rcslon3-svg/DOGS2_v1/assets/photos/all_you_need.jpg

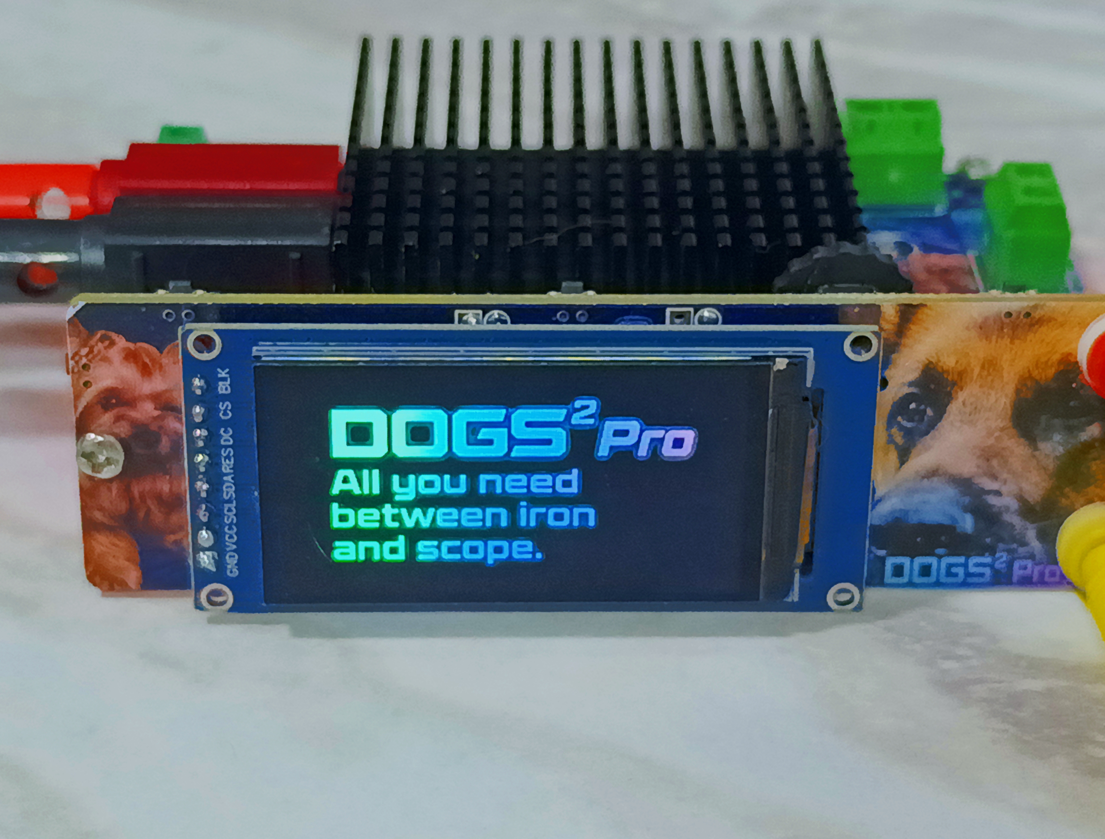
assets/photos/all_you_need.jpg
