rcslon3-svg/DOGS2_v1/assets/photos/connect.jpg

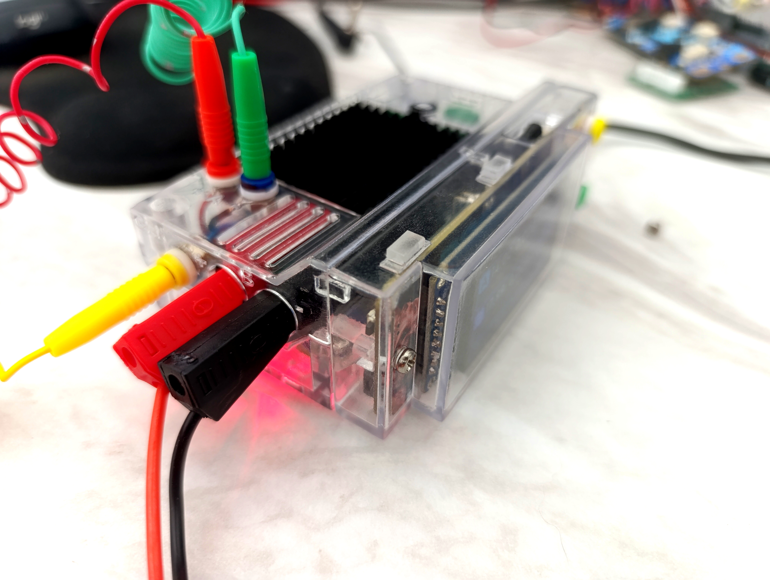
assets/photos/connect.jpg
