rcslon3-svg/DOGS2_v1/assets/photos/dogs2-signal-generator.jpg

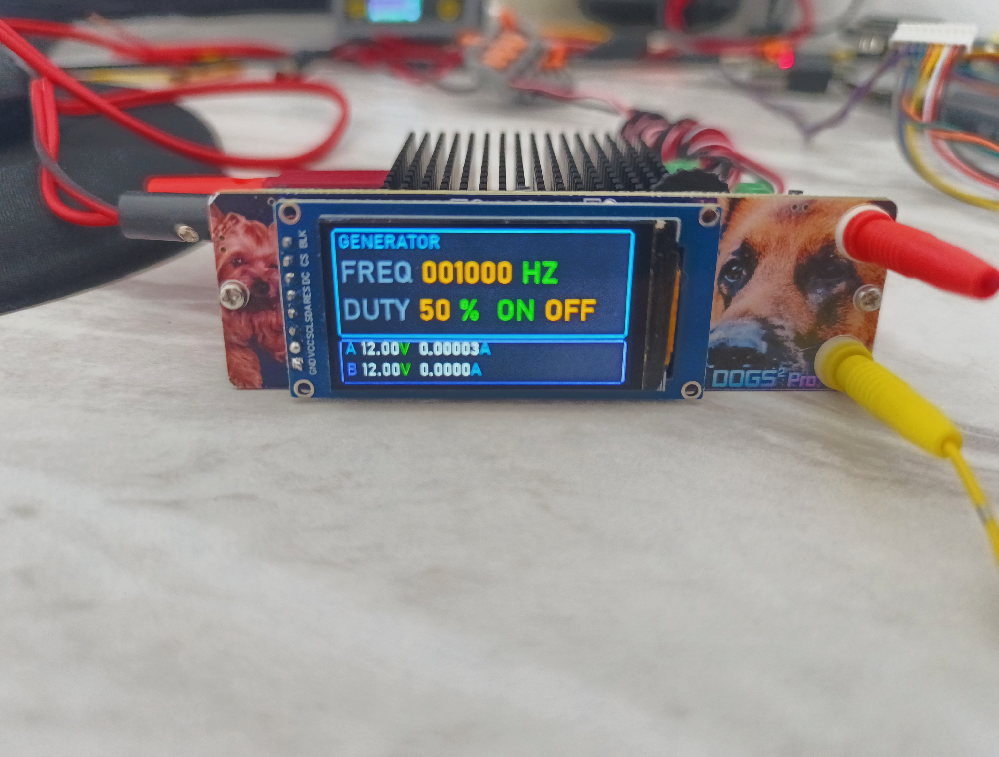
assets/photos/dogs2-signal-generator.jpg
