rcslon3-svg/DOGS2_v1/assets/photos/dogs2-working-prototype-front.png

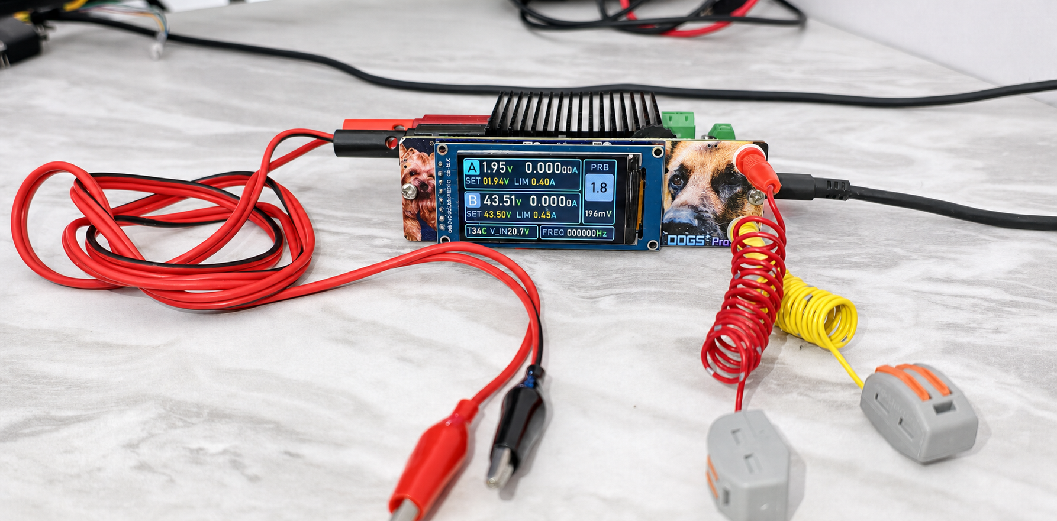
assets/photos/dogs2-working-prototype-front.png
