rcslon3-svg/DOGS2_v1/assets/photos/generator_display.jpg

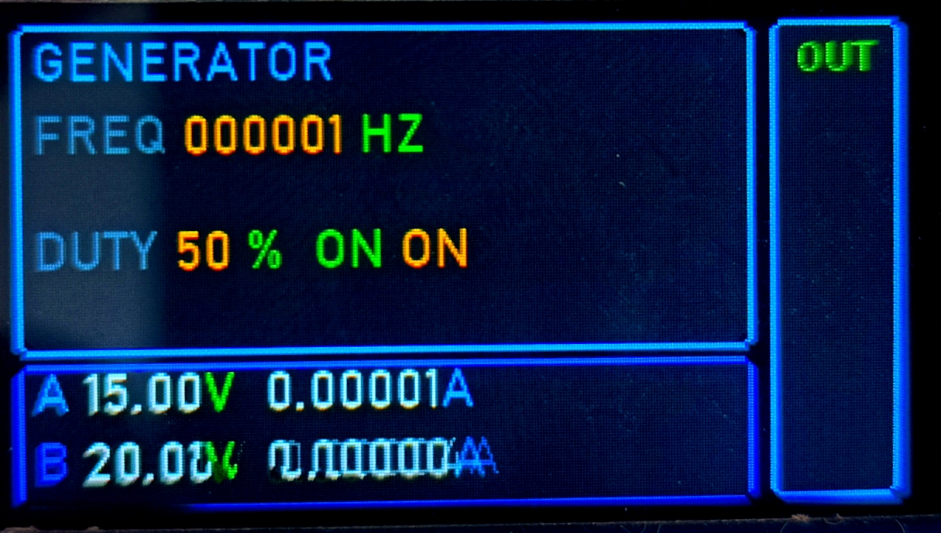
assets/photos/generator_display.jpg
