rcslon3-svg/DOGS2_v1/assets/photos/power_bottom.jpg

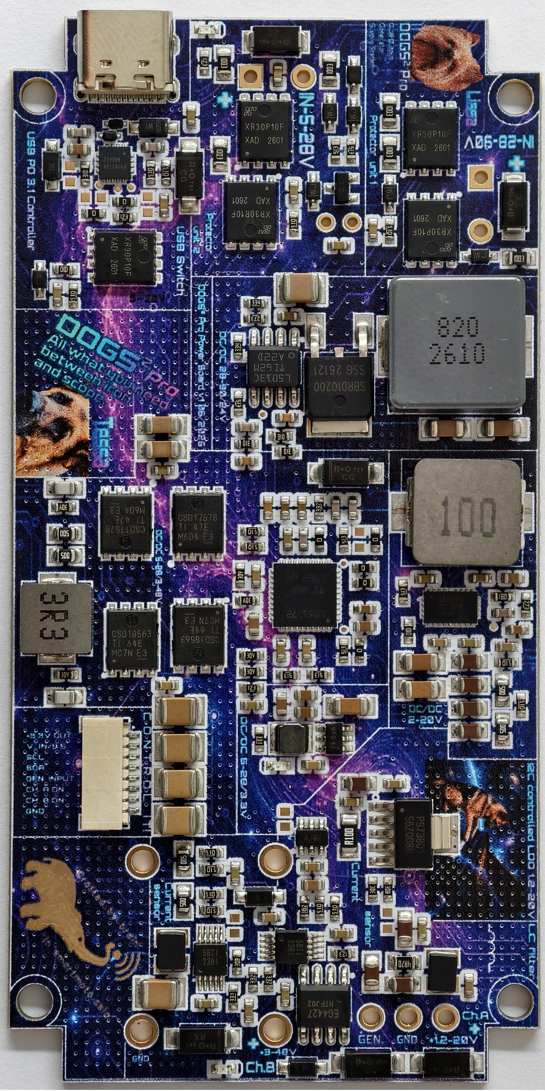
assets/photos/power_bottom.jpg
