rcslon3-svg/DOGS2_v1/assets/photos/power_bottom_90deg_40perc.jpg

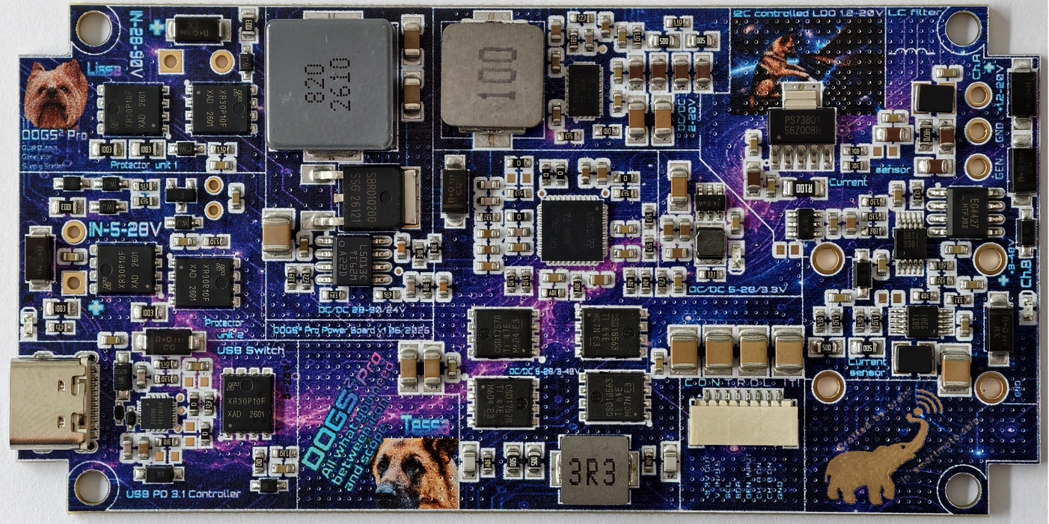
assets/photos/power_bottom_90deg_40perc.jpg
