rcslon3-svg/DOGS2_v1/assets/photos/power_source_display.jpg

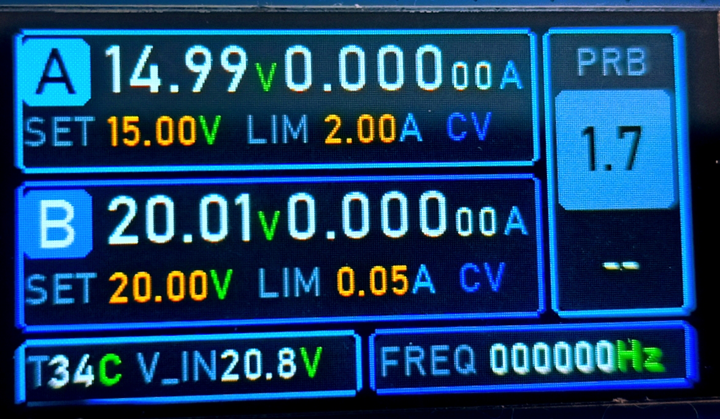
assets/photos/power_source_display.jpg
