rcslon3-svg/DOGS2_v1/assets/photos/rs485_display.jpg

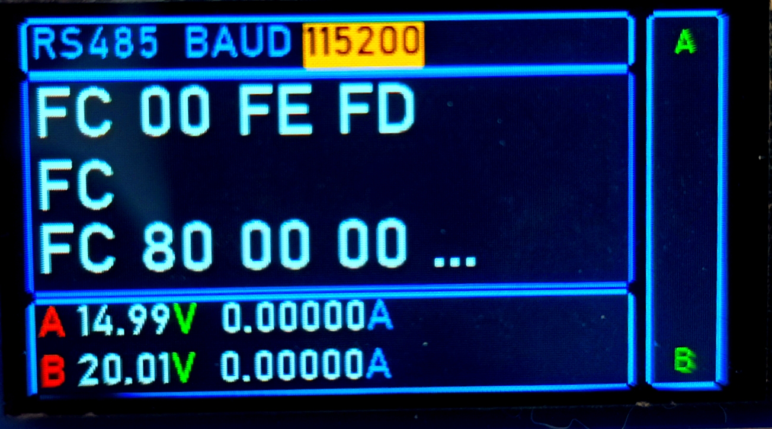
assets/photos/rs485_display.jpg
