rcslon3-svg/DOGS2_v1/assets/photos/uart_display.jpg

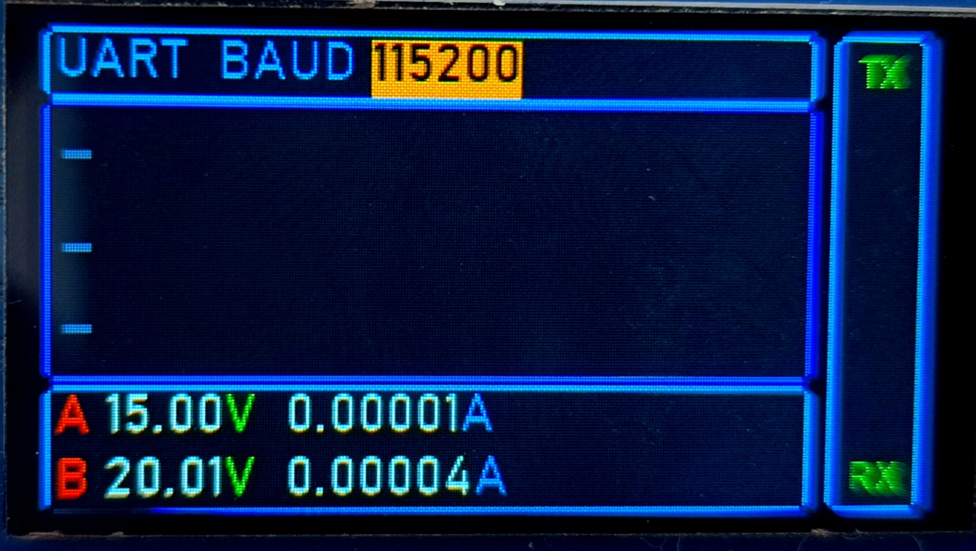
assets/photos/uart_display.jpg
