rcslon3-svg/DOGS2_v1/software/assets/dogs2-pro-all-you-need-transparent.png

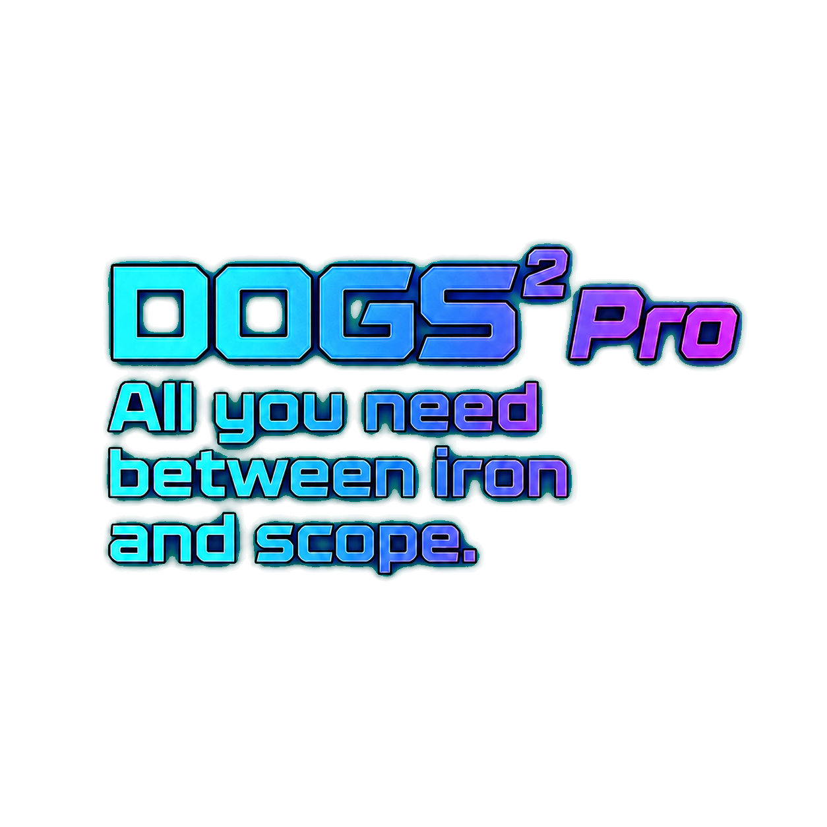
software/assets/dogs2-pro-all-you-need-transparent.png
