rcslon3-svg/DOGS2_v1/software/src/display.c

#include "display.h"

#include <stdarg.h>
#include <stdio.h>
#include <string.h>
#include "driver/gpio.h"
#include "driver/ledc.h"
#include "driver/spi_master.h"
#include "calibration.h"
#include "current_graph.h"
#include "esp_check.h"
#include "esp_log.h"
#include "esp_timer.h"
#include "freertos/FreeRTOS.h"
#include "freertos/task.h"
#include "probe_config.h"
#include "smooth_font.h"
#include "splash_bitmap.h"

#define RGB565(r, g, b) (uint16_t)((((r) & 0xF8U) << 8) | (((g) & 0xFCU) << 3) | ((b) >> 3))
#define COLOR_BLACK RGB565(0, 0, 0)
#define COLOR_WHITE RGB565(255, 255, 255)
#define COLOR_GREEN RGB565(40, 230, 90)
#define COLOR_RED RGB565(255, 45, 35)
#define COLOR_BLUE RGB565(30, 80, 255)
#define COLOR_YELLOW RGB565(255, 210, 0)
#define COLOR_CYAN RGB565(0, 210, 255)
#define COLOR_PURPLE RGB565(169, 92, 255)
#define COLOR_ORANGE RGB565(255, 120, 0)
#define COLOR_GRAY RGB565(155, 165, 180)
#define COLOR_LABEL RGB565(205, 215, 230)
#define COLOR_PANEL RGB565(9, 12, 18)
#define COLOR_BADGE_CV_FG COLOR_WHITE
#define COLOR_BADGE_CV_BG RGB565(18, 18, 18)
#define COLOR_BADGE_CC_FG COLOR_BLACK
#define COLOR_BADGE_CC_BG RGB565(0, 210, 220)
#define COLOR_ALERT_RED_FG COLOR_WHITE
#define COLOR_ALERT_RED_BG COLOR_RED
#define POWER_CHANNEL_FRAME_X 6
#define POWER_CHANNEL_FRAME_WIDTH 238
#define POWER_CHANNEL_INNER_X 8
#define POWER_CHANNEL_INNER_RIGHT 242
#define DISPLAY_CALIBRATION_SAMPLE_COUNT 32U
#define POWER_CURRENT_RIGHT 238
#define POWER_SIDE_FRAME_X 248
#define POWER_SIDE_FRAME_WIDTH 66
#define INTERFACE_MAIN_FRAME_WIDTH 268
#define INTERFACE_MAIN_INNER_RIGHT 272
#define INTERFACE_SIDE_FRAME_X 280
#define INTERFACE_SIDE_FRAME_WIDTH 34
#define INTERFACE_SIDE_INNER_X (INTERFACE_SIDE_FRAME_X + 2)
#define INTERFACE_SIDE_INNER_RIGHT \
    (INTERFACE_SIDE_FRAME_X + INTERFACE_SIDE_FRAME_WIDTH - 2)
#define CURRENT_GRAPH_X 10
#define CURRENT_GRAPH_Y 30
#define CURRENT_GRAPH_W 258
#define CURRENT_GRAPH_H 90
#define CURRENT_GRAPH_SAMPLES_PER_DIV 20
#define CURRENT_GRAPH_CELLS_Y 5
#define CURRENT_GRAPH_BASE_SAMPLE_MS 100U
#define TFT_BACKLIGHT_LEDC_MODE LEDC_HIGH_SPEED_MODE
#define TFT_BACKLIGHT_LEDC_TIMER LEDC_TIMER_3
#define TFT_BACKLIGHT_LEDC_CHANNEL LEDC_CHANNEL_7
#define TFT_BACKLIGHT_LEDC_RESOLUTION LEDC_TIMER_10_BIT
#define TFT_BACKLIGHT_LEDC_HZ 20000U
#define TFT_BACKLIGHT_DUTY_MAX ((1U << 10U) - 1U)
#define TFT_BACKLIGHT_FADE_MS 800U
#define TFT_BACKLIGHT_FADE_STEPS 32U
#define TFT_SPLASH_VISIBLE_MS 2000U
#define DISPLAY_BUFFER_ROWS 40U
#define DISPLAY_CURRENT_AVG_SAMPLES 3U

static spi_device_handle_t s_tft;
static const char *TAG = "display";
static int s_graph_slice_y;
static int s_graph_slice_h;

/*
 * Text is composed in RAM before it is sent to the TFT.  Besides allowing
 * four-bit antialiasing, this is important for a measurement instrument:
 * clearing and drawing a line in separate SPI operations made the old 5x7
 * font visibly blink.  A 320 x 40 buffer costs 25.6 kB but each completed
 * line now reaches the display as one continuous image.
 */
static uint16_t s_text_buffer[TFT_WIDTH * DISPLAY_BUFFER_ROWS];
static uint8_t s_fill_block[4096];

/* Match the pixel polarity already used by the working splash bitmap. */
static uint16_t display_pixel(uint16_t logical_color)
{
    uint16_t wire_color = (uint16_t)(logical_color ^ 0xFFFFU);
    return (uint16_t)((wire_color << 8) | (wire_color >> 8));
}

static void clear_text_buffer(int height, uint16_t logical_color)
{
    uint16_t pixel = display_pixel(logical_color);
    size_t count = (size_t)TFT_WIDTH * (size_t)height;
    for (size_t i = 0U; i < count; ++i) s_text_buffer[i] = pixel;
}

static uint32_t backlight_physical_duty(uint32_t logical_duty)
{
    if (logical_duty > TFT_BACKLIGHT_DUTY_MAX) logical_duty = TFT_BACKLIGHT_DUTY_MAX;
    return TFT_BACKLIGHT_ACTIVE_LEVEL ? logical_duty : (TFT_BACKLIGHT_DUTY_MAX - logical_duty);
}

static esp_err_t backlight_pwm_set(uint32_t logical_duty)
{
    esp_err_t err = ledc_set_duty(TFT_BACKLIGHT_LEDC_MODE,
                                  TFT_BACKLIGHT_LEDC_CHANNEL,
                                  backlight_physical_duty(logical_duty));
    if (err != ESP_OK) return err;
    return ledc_update_duty(TFT_BACKLIGHT_LEDC_MODE, TFT_BACKLIGHT_LEDC_CHANNEL);
}

static esp_err_t backlight_pwm_init(void)
{
    ledc_timer_config_t timer = {
        .speed_mode = TFT_BACKLIGHT_LEDC_MODE,
        .timer_num = TFT_BACKLIGHT_LEDC_TIMER,
        .duty_resolution = TFT_BACKLIGHT_LEDC_RESOLUTION,
        .freq_hz = TFT_BACKLIGHT_LEDC_HZ,
        .clk_cfg = LEDC_AUTO_CLK,
    };
    ESP_RETURN_ON_ERROR(ledc_timer_config(&timer), TAG, "backlight timer");

    ledc_channel_config_t channel = {
        .gpio_num = TFT_BACKLIGHT_GPIO,
        .speed_mode = TFT_BACKLIGHT_LEDC_MODE,
        .channel = TFT_BACKLIGHT_LEDC_CHANNEL,
        .intr_type = LEDC_INTR_DISABLE,
        .timer_sel = TFT_BACKLIGHT_LEDC_TIMER,
        .duty = backlight_physical_duty(0U),
        .hpoint = 0,
        .flags = {
            .output_invert = 0,
        },
    };
    return ledc_channel_config(&channel);
}

static void backlight_fade_in(void)
{
    const TickType_t step_delay = pdMS_TO_TICKS(TFT_BACKLIGHT_FADE_MS / TFT_BACKLIGHT_FADE_STEPS);
    for (uint32_t step = 0U; step <= TFT_BACKLIGHT_FADE_STEPS; ++step) {
        uint32_t duty = (TFT_BACKLIGHT_DUTY_MAX * step) / TFT_BACKLIGHT_FADE_STEPS;
        esp_err_t err = backlight_pwm_set(duty);
        if (err != ESP_OK) {
            ESP_LOGE(TAG, "backlight duty: %s", esp_err_to_name(err));
            return;
        }
        if (step < TFT_BACKLIGHT_FADE_STEPS) vTaskDelay(step_delay);
    }
}

static void log_pin_levels(const char *stage)
{
    ESP_LOGI(TAG, "%s pins: SCL=%d SDA=%d RES=%d DC=%d CS=%d BLK=%d",
             stage,
             gpio_get_level(TFT_SCLK_GPIO),
             gpio_get_level(TFT_MOSI_GPIO),
             gpio_get_level(TFT_RESET_GPIO),
             gpio_get_level(TFT_DC_GPIO),
             gpio_get_level(TFT_CS_GPIO),
             gpio_get_level(TFT_BACKLIGHT_GPIO));
}

/* send
 * Inputs: data selects command/data mode; bytes/length point to SPI payload.
 * Returns: none.
 * Does: sends one blocking SPI transaction to the TFT.
 */
static void send(bool data, const void *bytes, size_t length)
{
    if (s_tft == NULL) return;
    gpio_set_level(TFT_DC_GPIO, data ? 1 : 0);
    spi_transaction_t transaction = {
        .length = length * 8U,
        .tx_buffer = bytes
    };
    esp_err_t err = spi_device_polling_transmit(s_tft, &transaction);
    if (err != ESP_OK) ESP_LOGE(TAG, "spi tx: %s", esp_err_to_name(err));
}

/* command
 * Inputs: value is one ST7789 command byte.
 * Returns: none.
 * Does: sends a display command byte without parameters.
 */
static void command(uint8_t value)
{
    send(false, &value, 1U);
}

/* command_data
 * Inputs: cmd is the command byte; data/length are optional parameters.
 * Returns: none.
 * Does: sends one ST7789 command followed by its data bytes.
 */
static void command_data(uint8_t cmd, const uint8_t *data, size_t length)
{
    command(cmd);
    if (length != 0U) send(true, data, length);
}

/* set_window
 * Inputs: x/y/width/height describe the rectangular TFT write area.
 * Returns: none.
 * Does: programs the ST7789 column/page address window.
 */
static void set_window(int x, int y, int width, int height)
{
    x += TFT_X_OFFSET;
    y += TFT_Y_OFFSET;
    uint16_t x2 = (uint16_t)(x + width - 1);
    uint16_t y2 = (uint16_t)(y + height - 1);
    uint8_t cols[] = {(uint8_t)(x >> 8), (uint8_t)x, (uint8_t)(x2 >> 8), (uint8_t)x2};
    uint8_t rows[] = {(uint8_t)(y >> 8), (uint8_t)y, (uint8_t)(y2 >> 8), (uint8_t)y2};
    command_data(0x2A, cols, sizeof(cols));
    command_data(0x2B, rows, sizeof(rows));
    command(0x2C);
}

/* fill_rect
 * Inputs: rectangle coordinates and RGB565 color.
 * Returns: none.
 * Does: fills a rectangular TFT area with one solid color.
 */
static void fill_rect(int x, int y, int width, int height, uint16_t color)
{
    if (s_tft == NULL || width <= 0 || height <= 0) return;
    uint16_t wire_color = (uint16_t)(color ^ 0xFFFFU);
    for (size_t i = 0; i < sizeof(s_fill_block); i += 2U) {
        s_fill_block[i] = (uint8_t)(wire_color >> 8);
        s_fill_block[i + 1U] = (uint8_t)wire_color;
    }
    set_window(x, y, width, height);
    size_t remaining = (size_t)width * (size_t)height * 2U;
    gpio_set_level(TFT_DC_GPIO, 1);
    while (remaining != 0U) {
        size_t amount = remaining > sizeof(s_fill_block) ? sizeof(s_fill_block) : remaining;
        spi_transaction_t transaction = {.length = amount * 8U, .tx_buffer = s_fill_block};
        esp_err_t err = spi_device_polling_transmit(s_tft, &transaction);
        if (err != ESP_OK) {
            ESP_LOGE(TAG, "fill tx: %s", esp_err_to_name(err));
            return;
        }
        remaining -= amount;
    }
}

/* fill_round_rect
 * Inputs: rectangle, small corner radius and RGB565 color.
 * Returns: none.
 * Does: builds a compact rounded panel from horizontal spans; intended for the
 * small radii used by the 320x170 instrument UI.
 */
static void fill_round_rect(int x, int y, int width, int height, int radius, uint16_t color)
{
    if (radius <= 0 || width <= radius * 2 || height <= radius * 2) {
        fill_rect(x, y, width, height, color);
        return;
    }

    fill_rect(x, y + radius, width, height - radius * 2, color);
    for (int row = 0; row < radius; ++row) {
        int inset = radius - row;
        fill_rect(x + inset, y + row, width - inset * 2, 1, color);
        fill_rect(x + inset, y + height - 1 - row, width - inset * 2, 1, color);
    }
}

/* draw_panel_outline
 * Draws a continuous two-pixel panel outline with slightly clipped corners.
 */
static void draw_panel_outline(int x, int y, int width, int height, uint16_t color)
{
    const int thickness = 2;
    const int corner = 3;

    fill_rect(x + corner, y, width - corner * 2, thickness, color);
    fill_rect(x + corner, y + height - thickness,
              width - corner * 2, thickness, color);
    fill_rect(x, y + corner, thickness, height - corner * 2, color);
    fill_rect(x + width - thickness, y + corner,
              thickness, height - corner * 2, color);
    fill_rect(x + 1, y + 2, 2, 1, color);
    fill_rect(x + width - 3, y + 2, 2, 1, color);
    fill_rect(x + 1, y + height - 3, 2, 1, color);
    fill_rect(x + width - 3, y + height - 3, 2, 1, color);
}

/* draw_splash_bitmap
 * Inputs: none.
 * Returns: none.
 * Does: sends the pre-rendered 320x170 RGB565 startup splash to the TFT.
 */
static void draw_splash_bitmap(void)
{
    if (s_tft == NULL) return;
    if (SPLASH_BITMAP_WIDTH != TFT_WIDTH || SPLASH_BITMAP_HEIGHT != TFT_HEIGHT) {
        ESP_LOGE(TAG, "splash size mismatch: %ux%u for TFT %dx%d",
                 (unsigned)SPLASH_BITMAP_WIDTH,
                 (unsigned)SPLASH_BITMAP_HEIGHT,
                 TFT_WIDTH,
                 TFT_HEIGHT);
        return;
    }

    set_window(0, 0, TFT_WIDTH, TFT_HEIGHT);
    gpio_set_level(TFT_DC_GPIO, 1);
    const uint8_t *bytes = splash_bitmap_rgb565;
    size_t remaining = splash_bitmap_rgb565_size;
    while (remaining != 0U) {
        size_t amount = remaining > sizeof(s_fill_block) ? sizeof(s_fill_block) : remaining;
        for (size_t i = 0U; i < amount; i += 2U) {
            uint16_t pixel = (uint16_t)((uint16_t)bytes[i] << 8) | bytes[i + 1U];
            pixel ^= 0xFFFFU;
            s_fill_block[i] = (uint8_t)(pixel >> 8);
            s_fill_block[i + 1U] = (uint8_t)pixel;
        }
        spi_transaction_t transaction = {.length = amount * 8U, .tx_buffer = s_fill_block};
        esp_err_t err = spi_device_polling_transmit(s_tft, &transaction);
        if (err != ESP_OK) {
            ESP_LOGE(TAG, "splash tx: %s", esp_err_to_name(err));
            return;
        }
        bytes += amount;
        remaining -= amount;
    }
}

/* blend_on_black
 * Inputs: RGB565 color and 4-bit alpha value.
 * Returns: byte-swapped RGB565 pixel blended over black.
 * Does: prepares antialiased font pixels for direct TFT transfer.
 */
static uint16_t blend_on_black(uint16_t color, uint8_t alpha)
{
    uint16_t red = (uint16_t)(((color >> 11) & 0x1FU) * alpha / 15U);
    uint16_t green = (uint16_t)(((color >> 5) & 0x3FU) * alpha / 15U);
    uint16_t blue = (uint16_t)((color & 0x1FU) * alpha / 15U);
    uint16_t pixel = (uint16_t)((red << 11) | (green << 5) | blue);
    /* ST7789 receives the high byte first, while ESP32 RAM is little-endian. */
    return display_pixel(pixel);
}

/* blend_rgb565
 * Inputs: foreground and background RGB565 colors, and 4-bit alpha.
 * Returns: byte-swapped RGB565 pixel blended over the requested background.
 * Does: prepares antialiased font pixels when a highlighted background is used.
 */
static uint16_t blend_rgb565(uint16_t foreground, uint16_t background, uint8_t alpha)
{
    uint16_t fr = (foreground >> 11) & 0x1FU;
    uint16_t fg = (foreground >> 5) & 0x3FU;
    uint16_t fb = foreground & 0x1FU;
    uint16_t br = (background >> 11) & 0x1FU;
    uint16_t bg = (background >> 5) & 0x3FU;
    uint16_t bb = background & 0x1FU;

    uint16_t red = (uint16_t)((fr * alpha + br * (15U - alpha)) / 15U);
    uint16_t green = (uint16_t)((fg * alpha + bg * (15U - alpha)) / 15U);
    uint16_t blue = (uint16_t)((fb * alpha + bb * (15U - alpha)) / 15U);
    uint16_t pixel = (uint16_t)((red << 11) | (green << 5) | blue);
    return display_pixel(pixel);
}

/* send_text_buffer
 * Inputs: y is the top screen coordinate; height is the buffered line height.
 * Returns: none.
 * Does: sends the prepared full-width text buffer to the TFT.
 */
static void send_text_buffer(int y, int height)
{
    if (s_tft == NULL) return;
    set_window(0, y, TFT_WIDTH, height);
    gpio_set_level(TFT_DC_GPIO, 1);
    const uint8_t *bytes = (const uint8_t *)s_text_buffer;
    size_t remaining = (size_t)TFT_WIDTH * (size_t)height * 2U;
    while (remaining != 0U) {
        size_t amount = remaining > 4096U ? 4096U : remaining;
        spi_transaction_t transaction = {.length = amount * 8U, .tx_buffer = bytes};
        esp_err_t err = spi_device_polling_transmit(s_tft, &transaction);
        if (err != ESP_OK) {
            ESP_LOGE(TAG, "text tx: %s", esp_err_to_name(err));
            return;
        }
        bytes += amount;
        remaining -= amount;
    }
}

static void send_text_buffer_region(int x, int y, int width, int height)
{
    if (s_tft == NULL || width <= 0 || height <= 0) return;
    set_window(x, y, width, height);
    gpio_set_level(TFT_DC_GPIO, 1);
    for (int row = 0; row < height; ++row) {
        const uint8_t *bytes = (const uint8_t *)&s_text_buffer[row * TFT_WIDTH + x];
        spi_transaction_t transaction = {
            .length = (size_t)width * 2U * 8U,
            .tx_buffer = bytes
        };
        esp_err_t err = spi_device_polling_transmit(s_tft, &transaction);
        if (err != ESP_OK) {
            ESP_LOGE(TAG, "text region tx: %s", esp_err_to_name(err));
            return;
        }
    }
}

static void send_text_buffer_region_slice(int x, int y, int width,
                                          int first_row, int row_count)
{
    if (s_tft == NULL || width <= 0 || row_count <= 0) return;
    set_window(x, y, width, row_count);
    gpio_set_level(TFT_DC_GPIO, 1);
    for (int row = 0; row < row_count; ++row) {
        const uint8_t *bytes = (const uint8_t *)&s_text_buffer[
            (first_row + row) * TFT_WIDTH + x];
        spi_transaction_t transaction = {
            .length = (size_t)width * 2U * 8U,
            .tx_buffer = bytes
        };
        esp_err_t err = spi_device_polling_transmit(s_tft, &transaction);
        if (err != ESP_OK) {
            ESP_LOGE(TAG, "text slice tx: %s", esp_err_to_name(err));
            return;
        }
    }
}

/* draw_text
 * Inputs: x/y position, zero-terminated text, font pointer and RGB565 color.
 * Returns: none.
 * Does: renders one antialiased text line into RAM and transfers it as one
 * image to avoid flicker.
 */
static void draw_text(int x, int y, const char *text, const smooth_font_t *font, uint16_t color)
{
    int height = font->line_height;
    if (height > 40) height = 40;
    clear_text_buffer(height, COLOR_BLACK);

    int cursor = x;
    while (*text != '\0' && cursor < TFT_WIDTH) {
        uint8_t code = (uint8_t)*text++;
        if (code < font->first_char || code > font->last_char) code = (uint8_t)'?';
        const smooth_glyph_t *g = &font->glyphs[code - font->first_char];
        unsigned pixel_index = 0U;
        for (int row = 0; row < g->height; ++row) {
            int target_y = row + g->y_offset;
            for (int column = 0; column < g->width; ++column, ++pixel_index) {
                int target_x = cursor + g->x_offset + column;
                uint8_t packed = font->bitmap[g->bitmap_offset + pixel_index / 2U];
                uint8_t alpha = (pixel_index & 1U) == 0U ? packed >> 4 : packed & 0x0FU;
                if (alpha != 0U && target_x >= 0 && target_x < TFT_WIDTH &&
                    target_y >= 0 && target_y < height)
                    s_text_buffer[target_y * TFT_WIDTH + target_x] = blend_on_black(color, alpha);
            }
        }
        cursor += g->advance;
    }
    send_text_buffer(y, height);
}

/* draw_rich_text
 * Inputs:
 *   x/y   - text position;
 *   text  - zero-terminated ASCII string;
 *   font  - font used for all characters;
 *   fg/bg - per-character foreground and background colors.
 * Returns: none.
 * Does: draws one full-width line with optional per-character highlighting.
 */
static int compose_rich_text_on_panel(int x,
                                      const char *text,
                                      const smooth_font_t *font,
                                      const uint16_t *fg,
                                      const uint16_t *bg,
                                      uint16_t panel_background,
                                      int panel_left,
                                      int panel_right)
{
    int height = font->line_height;
    if (height > 40) height = 40;
    clear_text_buffer(height, COLOR_BLACK);

    if (panel_background != COLOR_BLACK) {
        uint16_t swapped = display_pixel(panel_background);
        if (panel_left < 0) panel_left = 0;
        if (panel_right > TFT_WIDTH) panel_right = TFT_WIDTH;
        for (int row = 0; row < height; ++row) {
            for (int column = panel_left; column < panel_right; ++column) {
                s_text_buffer[row * TFT_WIDTH + column] = swapped;
            }
        }
    }

    int cursor = x;
    size_t char_index = 0U;
    while (text[char_index] != '\0' && cursor < TFT_WIDTH) {
        uint8_t code = (uint8_t)text[char_index];
        if (code < font->first_char || code > font->last_char) code = (uint8_t)'?';
        const smooth_glyph_t *g = &font->glyphs[code - font->first_char];
        uint16_t foreground = fg[char_index];
        uint16_t background = bg[char_index] == COLOR_BLACK ? panel_background : bg[char_index];

        if (background != COLOR_BLACK) {
            int left = cursor;
            int right = cursor + g->advance;
            if (left < 0) left = 0;
            if (right > TFT_WIDTH) right = TFT_WIDTH;
            for (int row = 0; row < height; ++row) {
                for (int column = left; column < right; ++column) {
                    s_text_buffer[row * TFT_WIDTH + column] = display_pixel(background);
                }
            }
        }

        unsigned pixel_index = 0U;
        for (int row = 0; row < g->height; ++row) {
            int target_y = row + g->y_offset;
            for (int column = 0; column < g->width; ++column, ++pixel_index) {
                int target_x = cursor + g->x_offset + column;
                uint8_t packed = font->bitmap[g->bitmap_offset + pixel_index / 2U];
                uint8_t alpha = (pixel_index & 1U) == 0U ? packed >> 4 : packed & 0x0FU;
                if (alpha != 0U && target_x >= 0 && target_x < TFT_WIDTH &&
                    target_y >= 0 && target_y < height) {
                    s_text_buffer[target_y * TFT_WIDTH + target_x] =
                        blend_rgb565(foreground, background, alpha);
                }
            }
        }

        cursor += g->advance;
        ++char_index;
    }

    return height;
}

static void draw_rich_text_on_panel(int x,
                                    int y,
                                    const char *text,
                                    const smooth_font_t *font,
                                    const uint16_t *fg,
                                    const uint16_t *bg,
                                    uint16_t panel_background,
                                    int panel_left,
                                    int panel_right)
{
    int height = compose_rich_text_on_panel(x, text, font, fg, bg,
                                            panel_background, panel_left, panel_right);
    send_text_buffer_region(panel_left, y, panel_right - panel_left, height);
}

static void draw_rich_text_on_panel_clipped(int x,
                                            int y,
                                            const char *text,
                                            const smooth_font_t *font,
                                            const uint16_t *fg,
                                            const uint16_t *bg,
                                            uint16_t panel_background,
                                            int panel_left,
                                            int panel_right,
                                            int clip_top,
                                            int clip_bottom)
{
    int height = compose_rich_text_on_panel(x, text, font, fg, bg,
                                            panel_background, panel_left, panel_right);
    int first_row = clip_top > y ? clip_top - y : 0;
    int end_row = clip_bottom < y + height ? clip_bottom - y : height;
    if (end_row > first_row) {
        send_text_buffer_region_slice(panel_left, y + first_row,
                                      panel_right - panel_left,
                                      first_row, end_row - first_row);
    }
}

static void draw_rich_text(int x,
                           int y,
                           const char *text,
                           const smooth_font_t *font,
                           const uint16_t *fg,
                           const uint16_t *bg)
{
    draw_rich_text_on_panel(x, y, text, font, fg, bg, COLOR_BLACK, 0, TFT_WIDTH);
}

static int text_width(const char *text, const smooth_font_t *font)
{
    int width = 0;
    while (*text != '\0') {
        uint8_t code = (uint8_t)*text++;
        if (code < font->first_char || code > font->last_char) code = (uint8_t)'?';
        width += font->glyphs[code - font->first_char].advance;
    }
    return width;
}

static int text_visual_y(const char *text, const smooth_font_t *font,
                         int frame_y, int frame_height)
{
    int top = font->line_height;
    int bottom = 0;
    while (*text != '\0') {
        uint8_t code = (uint8_t)*text++;
        if (code < font->first_char || code > font->last_char) code = (uint8_t)'?';
        const smooth_glyph_t *glyph = &font->glyphs[code - font->first_char];
        if (glyph->height == 0U) continue;
        if (glyph->y_offset < top) top = glyph->y_offset;
        int glyph_bottom = glyph->y_offset + glyph->height;
        if (glyph_bottom > bottom) bottom = glyph_bottom;
    }
    if (bottom <= top) return frame_y + (frame_height - font->line_height) / 2;
    return frame_y + (frame_height - (bottom - top)) / 2 - top;
}

static void buffer_fill_rect(int x, int y, int width, int height,
                             int buffer_height, uint16_t color)
{
    uint16_t pixel = display_pixel(color);
    for (int row = y; row < y + height && row < buffer_height; ++row) {
        for (int column = x; column < x + width && column < TFT_WIDTH; ++column) {
            if (row >= 0 && column >= 0) s_text_buffer[row * TFT_WIDTH + column] = pixel;
        }
    }
}

static void buffer_fill_round_rect(int x, int y, int width, int height, int radius,
                                   int buffer_height, uint16_t color)
{
    buffer_fill_rect(x, y + radius, width, height - radius * 2, buffer_height, color);
    for (int row = 0; row < radius; ++row) {
        int inset = radius - row;
        buffer_fill_rect(x + inset, y + row, width - inset * 2, 1, buffer_height, color);
        buffer_fill_rect(x + inset, y + height - 1 - row,
                         width - inset * 2, 1, buffer_height, color);
    }
}

static void buffer_draw_text(int x, int y, const char *text, const smooth_font_t *font,
                             uint16_t foreground, uint16_t background, int buffer_height)
{
    int cursor = x;
    while (*text != '\0') {
        uint8_t code = (uint8_t)*text++;
        if (code < font->first_char || code > font->last_char) code = (uint8_t)'?';
        const smooth_glyph_t *g = &font->glyphs[code - font->first_char];
        unsigned pixel_index = 0U;
        for (int row = 0; row < g->height; ++row) {
            int target_y = y + row + g->y_offset;
            for (int column = 0; column < g->width; ++column, ++pixel_index) {
                int target_x = cursor + g->x_offset + column;
                uint8_t packed = font->bitmap[g->bitmap_offset + pixel_index / 2U];
                uint8_t alpha = (pixel_index & 1U) == 0U ? packed >> 4 : packed & 0x0FU;
                if (alpha != 0U && target_x >= 0 && target_x < TFT_WIDTH &&
                    target_y >= 0 && target_y < buffer_height) {
                    s_text_buffer[target_y * TFT_WIDTH + target_x] =
                        blend_rgb565(foreground, background, alpha);
                }
            }
        }
        cursor += g->advance;
    }
}

/* mark_range
 * Inputs: color arrays, start/length and colors to apply.
 * Returns: none.
 * Does: marks a substring as active on the settings display line.
 */
static void mark_range(uint16_t *fg,
                       uint16_t *bg,
                       size_t start,
                       size_t length,
                       uint16_t foreground,
                       uint16_t background)
{
    for (size_t i = start; i < start + length; ++i) {
        fg[i] = foreground;
        bg[i] = background;
    }
}

/* fill_text_colors
 * Inputs: per-character foreground/background arrays.
 * Returns: none.
 * Does: initializes a whole rich-text line to the default UI colors.
 */
static void fill_text_colors(uint16_t *fg, uint16_t *bg, size_t count)
{
    for (size_t i = 0; i < count; ++i) {
        fg[i] = COLOR_WHITE;
        bg[i] = COLOR_BLACK;
    }
}

/* append_colored
 * Inputs:
 *   line/fg/bg/pos - rich text buffer and current write position;
 *   text           - zero-terminated text to append;
 *   color          - foreground color for appended characters.
 * Returns: none.
 * Does: appends one colored text fragment to a rich-text line.
 */
static void append_colored(char *line,
                           uint16_t *fg,
                           uint16_t *bg,
                           size_t *pos,
                           const char *text,
                           uint16_t color)
{
    while (*text != '\0' && *pos < 63U) {
        line[*pos] = *text++;
        fg[*pos] = color;
        bg[*pos] = COLOR_BLACK;
        ++(*pos);
    }
    line[*pos] = '\0';
}

/* append_format_colored
 * Inputs: rich text buffer, color and printf-style format.
 * Returns: none.
 * Does: formats a short fragment and appends it with one color.
 */
static void append_format_colored(char *line,
                                  uint16_t *fg,
                                  uint16_t *bg,
                                  size_t *pos,
                                  uint16_t color,
                                  const char *format,
                                  ...)
{
    char fragment[24];
    va_list args;
    va_start(args, format);
    vsnprintf(fragment, sizeof(fragment), format, args);
    va_end(args);
    append_colored(line, fg, bg, pos, fragment, color);
}

/* draw_channel_actual_line
 * Inputs: screen row, channel letter and measured INA channel.
 * Returns: none.
 * Does: draws the large "actual output" line: channel, voltage and current.
 */
static uint8_t measured_current_decimals(char channel)
{
    (void)channel;
    return 5U;
}

typedef struct {
    int64_t samples[DISPLAY_CURRENT_AVG_SAMPLES];
    int64_t sum;
    uint8_t next;
    uint8_t count;
    bool initialized;
} display_current_filter_t;

static display_current_filter_t s_display_current_filter[2];

static int font_max_digit_width(const smooth_font_t *font);
static void buffer_draw_fixed_current_char(int x,
                                           int y,
                                           int slot_width,
                                           char c,
                                           const smooth_font_t *font,
                                           uint16_t fg,
                                           uint16_t bg,
                                           int buffer_height);

static int64_t measured_current_ua(char channel, const app_ina238_channel_t *measurement)
{
    if (!measurement->valid || measurement->shunt_uohm == 0U) return 0;
    int64_t current_ua = measurement->current_ua;
    uint8_t cal_channel = channel == 'A' ? CALIBRATION_CHANNEL_A : CALIBRATION_CHANNEL_B;
    if (calibration_current_available(cal_channel)) {
        return calibration_correct_current_ua(cal_channel, measurement->bus_mv, current_ua);
    }
    if (channel == 'A') {
        current_ua -= ((int64_t)measurement->bus_mv * CHANNEL_A_DIVIDER_LEAK_UA_PER_MV_NUM +
                       CHANNEL_A_DIVIDER_LEAK_UA_PER_MV_DEN / 2LL) /
                      CHANNEL_A_DIVIDER_LEAK_UA_PER_MV_DEN;
    }
    return current_ua;
}

static int64_t display_filtered_current_ua(char channel,
                                           const app_ina238_channel_t *measurement,
                                           int64_t current_ua)
{
    uint8_t index = channel == 'A' ? 0U : 1U;
    display_current_filter_t *filter = &s_display_current_filter[index];

    if (!measurement->valid) {
        memset(filter, 0, sizeof(*filter));
        return 0;
    }

    if (filter->count < DISPLAY_CURRENT_AVG_SAMPLES) {
        filter->samples[filter->next] = current_ua;
        filter->sum += current_ua;
        ++filter->count;
    } else {
        filter->sum -= filter->samples[filter->next];
        filter->samples[filter->next] = current_ua;
        filter->sum += current_ua;
    }
    filter->next = (uint8_t)((filter->next + 1U) % DISPLAY_CURRENT_AVG_SAMPLES);
    filter->initialized = true;

    if (filter->sum >= 0) return (filter->sum + filter->count / 2U) / filter->count;
    return -((-filter->sum + filter->count / 2U) / filter->count);
}

static void format_measured_current(char *out,
                                    size_t size,
                                    char channel,
                                    const app_ina238_channel_t *measurement)
{
    int64_t current_ua = measured_current_ua(channel, measurement);
    current_ua = display_filtered_current_ua(channel, measurement, current_ua);
    if (current_ua < 0) current_ua = 0;
    uint8_t decimals = measured_current_decimals(channel);
    int64_t scale = 1;
    for (uint8_t i = 0; i < decimals; ++i) scale *= 10LL;

    int64_t scaled = (current_ua * scale + 500000LL) / 1000000LL;
    int64_t whole = scaled / scale;
    int64_t frac = scaled % scale;

    if (decimals == 3U) {
        snprintf(out, size, "%lld.%03lld", (long long)whole, (long long)frac);
    } else if (decimals == 4U) {
        snprintf(out, size, "%lld.%04lld", (long long)whole, (long long)frac);
    } else if (decimals == 6U) {
        snprintf(out, size, "%lld.%06lld", (long long)whole, (long long)frac);
    } else {
        snprintf(out, size, "%lld.%05lld", (long long)whole, (long long)frac);
    }
}

/* draw_power_screen_frame
 * Inputs: none.
 * Returns: none.
 * Does: draws the static Twin Rail structure.  Thin cyan/purple rules echo the
 * startup logo without consuming space needed by the live measurements.
 */
static void draw_power_screen_frame(void)
{
    fill_round_rect(POWER_CHANNEL_INNER_X, 4,
                    POWER_CHANNEL_INNER_RIGHT - POWER_CHANNEL_INNER_X,
                    60, 4, COLOR_PANEL);
    draw_panel_outline(POWER_CHANNEL_FRAME_X, 2,
                       POWER_CHANNEL_FRAME_WIDTH, 64, COLOR_CYAN);
    fill_round_rect(POWER_CHANNEL_INNER_X, 72,
                    POWER_CHANNEL_INNER_RIGHT - POWER_CHANNEL_INNER_X,
                    62, 4, COLOR_PANEL);
    draw_panel_outline(POWER_CHANNEL_FRAME_X, 70,
                       POWER_CHANNEL_FRAME_WIDTH, 66, COLOR_PURPLE);
    fill_round_rect(POWER_SIDE_FRAME_X + 2, 4,
                    POWER_SIDE_FRAME_WIDTH - 4, 130, 4, COLOR_PANEL);
    draw_panel_outline(POWER_SIDE_FRAME_X, 2,
                       POWER_SIDE_FRAME_WIDTH, 134, COLOR_CYAN);

    fill_round_rect(8, 142, 148, 25, 4, COLOR_PANEL);
    draw_panel_outline(6, 140, 152, 29, COLOR_CYAN);
    fill_round_rect(164, 142, 148, 25, 4, COLOR_PANEL);
    draw_panel_outline(162, 140, 152, 29, COLOR_PURPLE);
}

static void draw_channel_actual_line(int y,
                                     char channel,
                                     const app_ina238_channel_t *measurement,
                                     bool cc_active,
                                     bool channel_enabled)
{
    const int height = 38;
    char voltage[16];
    char current[32];
    uint16_t channel_bg = channel == 'A' ? COLOR_CYAN : COLOR_PURPLE;
    uint16_t channel_fg = channel == 'A' ? COLOR_BLACK : COLOR_WHITE;
    if (!channel_enabled) {
        channel_bg = COLOR_GRAY;
        channel_fg = COLOR_BLACK;
    }

    if (measurement->valid) {
        snprintf(voltage, sizeof(voltage), "%.2f", (double)measurement->bus_mv / 1000.0);
        format_measured_current(current, sizeof(current), channel, measurement);
    } else {
        snprintf(voltage, sizeof(voltage), "--.--");
        snprintf(current, sizeof(current), "--.----");
    }

    clear_text_buffer(height, COLOR_BLACK);
    buffer_fill_rect(POWER_CHANNEL_INNER_X, 0,
                     POWER_CHANNEL_INNER_RIGHT - POWER_CHANNEL_INNER_X,
                     height, height, COLOR_PANEL);

    int old_badge_width = text_width(" A ", &instrument_30);
    int badge_width = (old_badge_width * 4 + 2) / 5;
    int badge_height = (instrument_30.line_height * 4 + 2) / 5;
    buffer_fill_round_rect(8, 0, badge_width, badge_height, 3, height, channel_bg);
    char channel_text[2] = {channel, '\0'};
    const smooth_glyph_t *channel_glyph =
        &instrument_30.glyphs[(uint8_t)channel - instrument_30.first_char];
    int channel_x = 8 + (badge_width - channel_glyph->width) / 2 - channel_glyph->x_offset;
    int channel_y = (badge_height - channel_glyph->height) / 2 - channel_glyph->y_offset;
    buffer_draw_text(channel_x, channel_y, channel_text, &instrument_30,
                     channel_fg, channel_bg, height);

    uint16_t value_color = (measurement->valid && channel_enabled) ? COLOR_WHITE : COLOR_GRAY;
    int voltage_x = 8 + badge_width + 6;
    buffer_draw_text(voltage_x, 0, voltage, &instrument_30,
                     value_color, COLOR_PANEL, height);
    int unit_v_x = voltage_x + text_width(voltage, &instrument_30) + 1;
    const smooth_glyph_t *main_zero =
        &instrument_30.glyphs[(uint8_t)'0' - instrument_30.first_char];
    const smooth_glyph_t *small_v =
        &instrument_18.glyphs[(uint8_t)'V' - instrument_18.first_char];
    int unit_v_y = (main_zero->y_offset + main_zero->height) -
                   (small_v->y_offset + small_v->height);
    buffer_draw_text(unit_v_x, unit_v_y, "V", &instrument_18,
                     channel_enabled ? COLOR_GREEN : COLOR_GRAY, COLOR_PANEL, height);

    size_t current_len = strlen(current);
    size_t small_digits = measurement->valid ? 2U : 0U;
    if (small_digits > current_len) small_digits = 0U;
    char current_main[32];
    char current_tail[4] = "";
    size_t main_len = current_len - small_digits;
    memcpy(current_main, current, main_len);
    current_main[main_len] = '\0';
    if (small_digits != 0U) snprintf(current_tail, sizeof(current_tail), "%s", current + main_len);
    uint16_t current_fg = (cc_active && channel_enabled) ? channel_fg : value_color;
    uint16_t current_bg = (cc_active && channel_enabled) ? channel_bg : COLOR_PANEL;

    int digit30_width = font_max_digit_width(&instrument_30);
    int dot30_width = text_width(".", &instrument_30);
    int digit18_width = font_max_digit_width(&instrument_18);
    int main_slots[5] = {
        digit30_width,
        dot30_width,
        digit30_width,
        digit30_width,
        digit30_width,
    };
    int fixed_current_width = main_slots[0] + main_slots[1] + main_slots[2] +
                              main_slots[3] + main_slots[4] +
                              digit18_width * 2;
    int unit_gap = 1;
    int current_group_width = fixed_current_width + unit_gap + text_width("A", &instrument_18);
    int current_x = POWER_CURRENT_RIGHT - current_group_width;
    int tail_x = current_x + main_slots[0] + main_slots[1] + main_slots[2] +
                 main_slots[3] + main_slots[4];
    if (cc_active && channel_enabled) {
        buffer_fill_round_rect(current_x - 2, 0, fixed_current_width + 4,
                               badge_height, 3, height, current_bg);
    }

    if (measurement->valid && main_len == 5U && strlen(current_tail) == 2U) {
        int x = current_x;
        for (size_t i = 0U; i < 5U; ++i) {
            buffer_draw_fixed_current_char(x, 0, main_slots[i], current_main[i],
                                           &instrument_30, current_fg, current_bg, height);
            x += main_slots[i];
        }
    } else {
        buffer_draw_text(current_x, 0, current_main, &instrument_30,
                         current_fg, current_bg, height);
        tail_x = current_x + text_width(current_main, &instrument_30);
    }

    const smooth_glyph_t *small_zero =
        &instrument_18.glyphs[(uint8_t)'0' - instrument_18.first_char];
    int tail_y = (main_zero->y_offset + main_zero->height) -
                 (small_zero->y_offset + small_zero->height);
    if (measurement->valid && strlen(current_tail) == 2U) {
        buffer_draw_fixed_current_char(tail_x, tail_y, digit18_width, current_tail[0],
                                       &instrument_18, current_fg, current_bg, height);
        buffer_draw_fixed_current_char(tail_x + digit18_width, tail_y, digit18_width,
                                       current_tail[1], &instrument_18,
                                       current_fg, current_bg, height);
    } else {
        buffer_draw_text(tail_x, tail_y, current_tail, &instrument_18,
                         current_fg, current_bg, height);
    }
    int unit_a_x = current_x + fixed_current_width + unit_gap;
    const smooth_glyph_t *small_a =
        &instrument_18.glyphs[(uint8_t)'A' - instrument_18.first_char];
    int unit_a_y = (main_zero->y_offset + main_zero->height) -
                   (small_a->y_offset + small_a->height);
    buffer_draw_text(unit_a_x, unit_a_y, "A", &instrument_18,
                     channel_enabled ? COLOR_CYAN : COLOR_GRAY, COLOR_PANEL, height);

    send_text_buffer_region(POWER_CHANNEL_INNER_X, y,
                            POWER_CHANNEL_INNER_RIGHT - POWER_CHANNEL_INNER_X,
                            height);
}

static void format_voltage(char *out, size_t size, uint16_t mv);
static void format_current(char *out, size_t size, uint16_t ma);
static size_t editable_digit_offset(const char *value, uint8_t digit);

/* draw_channel_set_line
 * Inputs:
 *   y - screen row;
 *   target_mv/target_ma - channel setpoints;
 *   measurement - INA data for temperature;
 *   voltage_select/current_select - control indices owned by this channel;
 *   selected/digit - active editor position.
 * Returns: none.
 * Does: draws requested values directly under the channel. The selected
 * voltage/current and selected decimal digit are highlighted here, not in a
 * separate bottom editor.
 */
static void draw_channel_set_line(int y,
                                  uint16_t target_mv,
                                  uint16_t target_ma,
                                  uint8_t voltage_select,
                                  uint8_t current_select,
                                  uint8_t selected,
                                  uint8_t digit,
                                  bool edit_blink_on,
                                  bool cc_active)
{
    char line[64] = "";
    uint16_t fg[64];
    uint16_t bg[64];
    size_t pos = 0U;
    char voltage[8];
    char current[8];
    size_t voltage_start;
    size_t current_start;

    fill_text_colors(fg, bg, 64U);
    append_colored(line, fg, bg, &pos, "SET ", COLOR_GRAY);
    voltage_start = pos;
    format_voltage(voltage, sizeof(voltage), target_mv);
    append_colored(line, fg, bg, &pos, voltage, COLOR_YELLOW);
    append_colored(line, fg, bg, &pos, "V  ", COLOR_GREEN);
    append_colored(line, fg, bg, &pos, "LIM ", COLOR_GRAY);
    current_start = pos;
    format_current(current, sizeof(current), target_ma);
    append_colored(line, fg, bg, &pos, current, COLOR_YELLOW);
    append_colored(line, fg, bg, &pos, "A", COLOR_CYAN);
    append_colored(line, fg, bg, &pos, "  ", COLOR_GRAY);
    append_colored(line, fg, bg, &pos, cc_active ? "CC" : "CV",
                   cc_active ? COLOR_RED : COLOR_BLUE);

    if (selected == voltage_select) {
        if (digit == CONTROL_DIGIT_WHOLE) {
            mark_range(fg, bg, voltage_start, strlen(voltage), COLOR_BLACK, COLOR_YELLOW);
        } else if (edit_blink_on) {
            mark_range(fg, bg, voltage_start, strlen(voltage), COLOR_YELLOW, COLOR_BLACK);
            mark_range(fg, bg, voltage_start + editable_digit_offset(voltage, digit),
                       1U, COLOR_BLACK, COLOR_YELLOW);
        }
    } else if (selected == current_select) {
        if (digit == CONTROL_DIGIT_WHOLE || edit_blink_on) {
            mark_range(fg, bg, current_start, strlen(current), COLOR_BLACK, COLOR_YELLOW);
        }
    }
    draw_rich_text_on_panel(8, y, line, &instrument_18, fg, bg,
                            COLOR_PANEL,
                            POWER_CHANNEL_INNER_X, POWER_CHANNEL_INNER_RIGHT);
}

static void draw_compact_actual_line_to(int y,
                                        char channel,
                                        const app_ina238_channel_t *measurement,
                                        int panel_right)
{
    char line[64] = "";
    uint16_t fg[64];
    uint16_t bg[64];
    size_t pos = 0U;

    fill_text_colors(fg, bg, 64U);
    append_format_colored(line, fg, bg, &pos, COLOR_ORANGE, "%c ", channel);

    if (measurement->valid) {
        append_format_colored(line, fg, bg, &pos, COLOR_WHITE,
                              "%.2f", (double)measurement->bus_mv / 1000.0);
    } else {
        append_colored(line, fg, bg, &pos, "--.--", COLOR_GRAY);
    }
    append_colored(line, fg, bg, &pos, "V  ", COLOR_GREEN);

    if (measurement->valid) {
        char current[32];
        format_measured_current(current, sizeof(current), channel, measurement);
        append_colored(line, fg, bg, &pos, current, COLOR_WHITE);
    } else {
        append_colored(line, fg, bg, &pos, "--.--", COLOR_GRAY);
    }
    append_colored(line, fg, bg, &pos, "A", COLOR_CYAN);

    draw_rich_text_on_panel_clipped(10, y, line, &instrument_18, fg, bg,
                                    COLOR_PANEL, 8, panel_right,
                                    126, 167);
}

static void draw_bottom_actuals_to(const app_state_t *s, int panel_right)
{
    draw_compact_actual_line_to(126, 'A', &s->ina238.channel[0], panel_right);
    draw_compact_actual_line_to(148, 'B', &s->ina238.channel[1], panel_right);
}

static void draw_highlighted_value_line(int y,
                                        const char *label,
                                        const char *value,
                                        const char *suffix,
                                        uint8_t this_select,
                                        const app_state_t *s)
{
    char line[64] = "";
    uint16_t fg[64];
    uint16_t bg[64];
    size_t pos = 0U;
    size_t value_start;

    fill_text_colors(fg, bg, 64U);
    append_colored(line, fg, bg, &pos, label, COLOR_GRAY);
    append_colored(line, fg, bg, &pos, " ", COLOR_GRAY);
    value_start = pos;
    append_colored(line, fg, bg, &pos, value, COLOR_YELLOW);
    if (suffix != NULL && suffix[0] != '\0') {
        append_colored(line, fg, bg, &pos, " ", COLOR_GRAY);
        append_colored(line, fg, bg, &pos, suffix, COLOR_GREEN);
    }

    if (s->control.selected_value == this_select) {
        if (s->control.selected_digit == CONTROL_DIGIT_WHOLE) {
            mark_range(fg, bg, value_start, strlen(value), COLOR_BLACK, COLOR_YELLOW);
        } else {
            mark_range(fg, bg,
                       value_start + editable_digit_offset(value, s->control.selected_digit),
                       1U,
                       COLOR_BLACK,
                       COLOR_YELLOW);
        }
    }

    draw_rich_text(8, y, line, &instrument_30, fg, bg);
}

static void draw_generator_duty_line(const app_state_t *s)
{
    char line[64] = "";
    uint16_t fg[64];
    uint16_t bg[64];
    size_t pos = 0U;
    size_t duty_start;
    size_t on_start;
    char duty[8];
    const char *on_value = s->control.generator_on ? "ON" : "OFF";

    fill_text_colors(fg, bg, 64U);
    append_colored(line, fg, bg, &pos, "DUTY ", COLOR_GRAY);
    duty_start = pos;
    snprintf(duty, sizeof(duty), "%02u", (unsigned)s->control.generator_duty_percent);
    append_colored(line, fg, bg, &pos, duty, COLOR_YELLOW);
    append_colored(line, fg, bg, &pos, " %  ON ", COLOR_GREEN);
    on_start = pos;
    append_colored(line, fg, bg, &pos, on_value, COLOR_YELLOW);

    if (s->control.selected_value == CONTROL_SELECT_GEN_DUTY) {
        if (s->control.selected_digit == CONTROL_DIGIT_WHOLE) {
            mark_range(fg, bg, duty_start, strlen(duty), COLOR_BLACK, COLOR_YELLOW);
        } else if (((esp_timer_get_time() / 500000LL) & 1LL) == 0LL) {
            mark_range(fg, bg,
                       duty_start + editable_digit_offset(duty, s->control.selected_digit),
                       1U,
                       COLOR_BLACK,
                       COLOR_YELLOW);
        }
    } else if (s->control.selected_value == CONTROL_SELECT_GEN_ON) {
        bool blink_on = s->control.selected_digit == CONTROL_DIGIT_WHOLE ||
                        ((esp_timer_get_time() / 500000LL) & 1LL) == 0LL;
        if (blink_on) {
            mark_range(fg, bg, on_start, strlen(on_value), COLOR_BLACK, COLOR_YELLOW);
        }
    }

    draw_rich_text_on_panel(12, 72, line, &instrument_30, fg, bg,
                            COLOR_PANEL, 8, TFT_WIDTH - 8);
}

static void draw_generator_frequency_line(const app_state_t *s)
{
    char line[64] = "";
    char value[16];
    uint16_t fg[64];
    uint16_t bg[64];
    size_t pos = 0U;
    size_t value_start;

    fill_text_colors(fg, bg, 64U);
    append_colored(line, fg, bg, &pos, "FREQ ", COLOR_GRAY);
    value_start = pos;
    snprintf(value, sizeof(value), "%06lu", (unsigned long)s->control.generator_freq_hz);
    append_colored(line, fg, bg, &pos, value, COLOR_YELLOW);
    append_colored(line, fg, bg, &pos, " HZ", COLOR_GREEN);

    if (s->control.selected_value == CONTROL_SELECT_GEN_FREQ) {
        if (s->control.selected_digit == CONTROL_DIGIT_WHOLE) {
            mark_range(fg, bg, value_start, strlen(value), COLOR_BLACK, COLOR_YELLOW);
        } else if (((esp_timer_get_time() / 500000LL) & 1LL) == 0LL) {
            mark_range(fg, bg,
                       value_start + editable_digit_offset(value, s->control.selected_digit),
                       1U, COLOR_BLACK, COLOR_YELLOW);
        }
    }
    draw_rich_text_on_panel(12, 32, line, &instrument_30, fg, bg,
                            COLOR_PANEL, 8, TFT_WIDTH - 8);
}

static void draw_generator_actual_line(int y,
                                       char channel,
                                       const app_ina238_channel_t *measurement)
{
    char line[64] = "";
    uint16_t fg[64];
    uint16_t bg[64];
    size_t pos = 0U;
    uint16_t channel_color = channel == 'A' ? COLOR_CYAN : COLOR_PURPLE;

    fill_text_colors(fg, bg, 64U);
    append_format_colored(line, fg, bg, &pos, channel_color, "%c ", channel);
    if (measurement->valid) {
        append_format_colored(line, fg, bg, &pos, COLOR_WHITE,
                              "%.2f", (double)measurement->bus_mv / 1000.0);
    } else {
        append_colored(line, fg, bg, &pos, "--.--", COLOR_GRAY);
    }
    append_colored(line, fg, bg, &pos, "V  ", COLOR_GREEN);
    if (measurement->valid) {
        char current[32];
        format_measured_current(current, sizeof(current), channel, measurement);
        append_colored(line, fg, bg, &pos, current, COLOR_WHITE);
    } else {
        append_colored(line, fg, bg, &pos, "--.--", COLOR_GRAY);
    }
    append_colored(line, fg, bg, &pos, "A", COLOR_CYAN);
    draw_rich_text_on_panel(12, y, line, &instrument_18, fg, bg,
                            COLOR_PANEL, 8, TFT_WIDTH - 8);
}

static void draw_generator_screen(const app_state_t *s, bool draw_frame)
{
    if (draw_frame) {
        char title[] = "GENERATOR";
        uint16_t fg[16];
        uint16_t bg[16];
        fill_rect(0, 0, TFT_WIDTH, TFT_HEIGHT, COLOR_BLACK);
        fill_round_rect(8, 4, TFT_WIDTH - 16, 110, 4, COLOR_PANEL);
        draw_panel_outline(6, 2, TFT_WIDTH - 12, 114, COLOR_CYAN);
        fill_round_rect(8, 121, TFT_WIDTH - 16, 46, 4, COLOR_PANEL);
        draw_panel_outline(6, 119, TFT_WIDTH - 12, 50, COLOR_PURPLE);
        fill_text_colors(fg, bg, 16U);
        for (size_t i = 0U; title[i] != '\0'; ++i) fg[i] = COLOR_CYAN;
        draw_rich_text_on_panel(12, 7, title, &instrument_18, fg, bg,
                                COLOR_PANEL, 8, TFT_WIDTH - 8);
    }
    draw_generator_frequency_line(s);
    draw_generator_duty_line(s);
    draw_generator_actual_line(121, 'A', &s->ina238.channel[0]);
    draw_generator_actual_line(145, 'B', &s->ina238.channel[1]);
}

static void draw_interface_side_label(const char *label, int frame_y)
{
    uint16_t fg[8];
    uint16_t bg[8];
    size_t length = strlen(label);
    if (length == 0U) return;

    fill_text_colors(fg, bg, 8U);
    for (size_t i = 0U; i < length && i < 8U; ++i) fg[i] = COLOR_GREEN;
    int width = INTERFACE_SIDE_INNER_RIGHT - INTERFACE_SIDE_INNER_X;
    int x = INTERFACE_SIDE_INNER_X +
            (width - text_width(label, &instrument_14)) / 2;
    int y = text_visual_y(label, &instrument_14, frame_y, 20);
    draw_rich_text_on_panel_clipped(x, y, label, &instrument_14,
                                    fg, bg, COLOR_PANEL,
                                    INTERFACE_SIDE_INNER_X,
                                    INTERFACE_SIDE_INNER_RIGHT,
                                    frame_y - 1, frame_y + 21);
}

static void draw_interface_frame(bool masked_header,
                                 const char *top_label,
                                 const char *bottom_label)
{
    fill_rect(0, 0, TFT_WIDTH, TFT_HEIGHT, COLOR_BLACK);
    if (masked_header) {
        fill_rect(8, 3, INTERFACE_MAIN_FRAME_WIDTH - 4, 46, COLOR_PANEL);
        draw_panel_outline(6, 1, INTERFACE_MAIN_FRAME_WIDTH, 50, COLOR_CYAN);
        fill_rect(8, 54, INTERFACE_MAIN_FRAME_WIDTH - 4, 66, COLOR_PANEL);
        draw_panel_outline(6, 52, INTERFACE_MAIN_FRAME_WIDTH, 70, COLOR_PURPLE);
    } else {
        fill_rect(8, 3, INTERFACE_MAIN_FRAME_WIDTH - 4, 21, COLOR_PANEL);
        draw_panel_outline(6, 1, INTERFACE_MAIN_FRAME_WIDTH, 25, COLOR_CYAN);
        fill_rect(8, 28, INTERFACE_MAIN_FRAME_WIDTH - 4, 93, COLOR_PANEL);
        draw_panel_outline(6, 26, INTERFACE_MAIN_FRAME_WIDTH, 97, COLOR_PURPLE);
    }
    fill_rect(8, 126, INTERFACE_MAIN_FRAME_WIDTH - 4, 41, COLOR_PANEL);
    draw_panel_outline(6, 124, INTERFACE_MAIN_FRAME_WIDTH, 45, COLOR_CYAN);

    fill_rect(INTERFACE_SIDE_INNER_X, 3,
              INTERFACE_SIDE_INNER_RIGHT - INTERFACE_SIDE_INNER_X,
              164, COLOR_PANEL);
    draw_panel_outline(INTERFACE_SIDE_FRAME_X, 1,
                       INTERFACE_SIDE_FRAME_WIDTH, 168, COLOR_CYAN);
    draw_interface_side_label(top_label, 4);
    draw_interface_side_label(bottom_label, 146);
}

static void draw_serial_header(const app_state_t *s,
                               const char *title,
                               uint32_t rate,
                               uint8_t select,
                               int panel_right)
{
    char line[64] = "";
    char value[16];
    uint16_t fg[64];
    uint16_t bg[64];
    size_t pos = 0U;
    size_t baud_start;

    fill_text_colors(fg, bg, 64U);
    append_colored(line, fg, bg, &pos, title, COLOR_CYAN);
    append_colored(line, fg, bg, &pos, "  BAUD ", COLOR_CYAN);
    baud_start = pos;
    snprintf(value, sizeof(value), "%lu", (unsigned long)rate);
    append_colored(line, fg, bg, &pos, value, COLOR_YELLOW);

    if (s->control.selected_value == select) {
        bool blink_on = s->control.selected_digit == CONTROL_DIGIT_WHOLE ||
                        ((esp_timer_get_time() / 500000LL) & 1LL) == 0LL;
        if (blink_on) {
            mark_range(fg, bg, baud_start, strlen(value), COLOR_BLACK, COLOR_YELLOW);
        }
    }

    draw_rich_text_on_panel_clipped(10, 4, line, &instrument_18, fg, bg,
                                    COLOR_PANEL, 8, panel_right,
                                    3, 24);
}

static void draw_uart_rx_line(int y, const char *text, int panel_right)
{
    const char *shown = text[0] != '\0' ? text : "-";
    uint16_t fg[64];
    uint16_t bg[64];
    fill_text_colors(fg, bg, 64U);
    for (size_t i = 0U; shown[i] != '\0' && i < 64U; ++i) {
        fg[i] = text[0] != '\0' ? COLOR_WHITE : COLOR_GRAY;
    }
    draw_rich_text_on_panel_clipped(10, y, shown, &instrument_30, fg, bg,
                                    COLOR_PANEL, 8, panel_right,
                                    28, 121);
}

static void draw_small_rx_line(int y, const char *text, int panel_right)
{
    const char *shown = text[0] != '\0' ? text : "-";
    uint16_t fg[64];
    uint16_t bg[64];
    fill_text_colors(fg, bg, 64U);
    for (size_t i = 0U; shown[i] != '\0' && i < 64U; ++i) {
        fg[i] = text[0] != '\0' ? COLOR_WHITE : COLOR_GRAY;
    }
    draw_rich_text_on_panel_clipped(10, y, shown, &instrument_18, fg, bg,
                                    COLOR_PANEL, 8, panel_right,
                                    54, 120);
}

static void draw_serial_screen(const app_state_t *s, const char *title, uint32_t rate,
                               uint8_t select, bool draw_frame)
{
    if (draw_frame) {
        bool rs485 = strcmp(title, "RS485") == 0;
        draw_interface_frame(false,
                             rs485 ? "A" : "RX",
                             rs485 ? "B" : "TX");
    }
    draw_serial_header(s, title, rate, select, INTERFACE_MAIN_INNER_RIGHT);
    draw_uart_rx_line(28, s->uart.lines[0], INTERFACE_MAIN_INNER_RIGHT);
    draw_uart_rx_line(60, s->uart.lines[1], INTERFACE_MAIN_INNER_RIGHT);
    draw_uart_rx_line(88, s->uart.lines[2], INTERFACE_MAIN_INNER_RIGHT);
    draw_bottom_actuals_to(s, INTERFACE_MAIN_INNER_RIGHT);
}

static void draw_mask_line(int y,
                           const char *mask,
                           uint8_t select,
                           const app_state_t *s,
                           int panel_right)
{
    char line[32] = "";
    uint16_t fg[32];
    uint16_t bg[32];
    size_t pos = 0U;
    size_t value_start;

    fill_text_colors(fg, bg, 32U);
    append_colored(line, fg, bg, &pos, "MASK ", COLOR_CYAN);
    value_start = pos;
    append_colored(line, fg, bg, &pos, mask, COLOR_YELLOW);

    if (s->control.selected_value == select) {
        if (s->control.selected_digit == CONTROL_DIGIT_WHOLE) {
            mark_range(fg, bg, value_start, strlen(mask), COLOR_BLACK, COLOR_YELLOW);
        } else if (s->control.selected_digit < strlen(mask) &&
                   ((esp_timer_get_time() / 500000LL) & 1LL) == 0LL) {
            mark_range(fg, bg, value_start + s->control.selected_digit, 1U, COLOR_BLACK, COLOR_YELLOW);
        }
    }

    draw_rich_text_on_panel_clipped(10, y, line, &instrument_18, fg, bg,
                                    COLOR_PANEL, 8, panel_right,
                                    3, 49);
}

static void draw_masked_serial_frame(const char *top_label,
                                     const char *bottom_label)
{
    draw_interface_frame(true, top_label, bottom_label);
}

static void draw_serial_screen_with_mask(const app_state_t *s,
                                         const char *title,
                                         uint32_t rate,
                                         uint8_t rate_select,
                                         const char *mask,
                                         uint8_t mask_select,
                                         bool draw_frame)
{
    if (draw_frame) draw_masked_serial_frame("RX", "TX");
    draw_serial_header(s, title, rate, rate_select, INTERFACE_MAIN_INNER_RIGHT);
    draw_mask_line(27, mask, mask_select, s, INTERFACE_MAIN_INNER_RIGHT);
    draw_small_rx_line(54, s->uart.lines[0], INTERFACE_MAIN_INNER_RIGHT);
    draw_small_rx_line(76, s->uart.lines[1], INTERFACE_MAIN_INNER_RIGHT);
    draw_small_rx_line(98, s->uart.lines[2], INTERFACE_MAIN_INNER_RIGHT);
    draw_bottom_actuals_to(s, INTERFACE_MAIN_INNER_RIGHT);
}

static void draw_i2c_rx_line_to(int y, const char *text, int panel_right)
{
    const char *shown = text[0] != '\0' ? text : "-";
    uint16_t fg[64];
    uint16_t bg[64];
    fill_text_colors(fg, bg, 64U);
    for (size_t i = 0U; shown[i] != '\0' && i < 64U; ++i) {
        fg[i] = text[0] != '\0' ? COLOR_WHITE : COLOR_GRAY;
    }
    draw_rich_text_on_panel_clipped(10, y, shown, &instrument_18, fg, bg,
                                    COLOR_PANEL, 8, panel_right,
                                    28, 121);
}

static void draw_i2c_sniffer_screen(const app_state_t *s, bool draw_frame)
{
    char line[64] = "";
    uint16_t fg[64];
    uint16_t bg[64];
    size_t pos = 0U;
    size_t mask_start;

    if (draw_frame) {
        draw_interface_frame(false, "SDA", "SCL");
    }

    fill_text_colors(fg, bg, 64U);
    append_colored(line, fg, bg, &pos, "I2C SNIFFER  MASK ", COLOR_CYAN);
    mask_start = pos;
    append_colored(line, fg, bg, &pos, s->control.i2c_mask, COLOR_YELLOW);
    if (s->control.selected_value == CONTROL_SELECT_I2C_MASK) {
        if (s->control.selected_digit == CONTROL_DIGIT_WHOLE) {
            mark_range(fg, bg, mask_start, strlen(s->control.i2c_mask),
                       COLOR_BLACK, COLOR_YELLOW);
        } else if (s->control.selected_digit < strlen(s->control.i2c_mask) &&
                   ((esp_timer_get_time() / 500000LL) & 1LL) == 0LL) {
            mark_range(fg, bg, mask_start + s->control.selected_digit, 1U,
                       COLOR_BLACK, COLOR_YELLOW);
        }
    }
    draw_rich_text_on_panel_clipped(10, 4, line, &instrument_18, fg, bg,
                                    COLOR_PANEL, 8, INTERFACE_MAIN_INNER_RIGHT,
                                    3, 24);

    draw_i2c_rx_line_to(30, s->i2c_sniffer.lines[0], INTERFACE_MAIN_INNER_RIGHT);
    draw_i2c_rx_line_to(52, s->i2c_sniffer.lines[1], INTERFACE_MAIN_INNER_RIGHT);
    draw_i2c_rx_line_to(74, s->i2c_sniffer.lines[2], INTERFACE_MAIN_INNER_RIGHT);
    draw_i2c_rx_line_to(96, s->i2c_sniffer.lines[3], INTERFACE_MAIN_INNER_RIGHT);
    draw_bottom_actuals_to(s, INTERFACE_MAIN_INNER_RIGHT);
}

static void draw_i2c_master_screen(const app_state_t *s, bool draw_frame)
{
    char line[64] = "";
    uint16_t fg[64];
    uint16_t bg[64];
    size_t pos = 0U;

    if (draw_frame) {
        draw_interface_frame(false, "SDA", "SCL");
    }

    line[0] = '\0';
    pos = 0U;
    fill_text_colors(fg, bg, 64U);
    append_colored(line, fg, bg, &pos, "I2C MASTER  100K", COLOR_CYAN);
    draw_rich_text_on_panel_clipped(10, 4, line, &instrument_18, fg, bg,
                                    COLOR_PANEL, 8, INTERFACE_MAIN_INNER_RIGHT,
                                    3, 24);

    draw_i2c_rx_line_to(30, s->i2c_sniffer.lines[0], INTERFACE_MAIN_INNER_RIGHT);
    draw_i2c_rx_line_to(52, s->i2c_sniffer.lines[1], INTERFACE_MAIN_INNER_RIGHT);
    draw_i2c_rx_line_to(74, s->i2c_sniffer.lines[2], INTERFACE_MAIN_INNER_RIGHT);
    draw_i2c_rx_line_to(96, s->i2c_sniffer.lines[3], INTERFACE_MAIN_INNER_RIGHT);
    draw_bottom_actuals_to(s, INTERFACE_MAIN_INNER_RIGHT);
}

static void draw_can_screen(const app_state_t *s, bool draw_frame)
{
    static char previous_header[64];
    static char previous_status[64];
    static char previous_rx[3][I2C_DISPLAY_CHARS + 1U];
    static bool previous_header_selected;
    static uint8_t previous_header_digit;
    static uint8_t previous_header_blink;
    static bool previous_status_selected;
    static uint8_t previous_status_digit;
    static uint8_t previous_status_blink;
    char line[64] = "";
    char value[16];
    uint16_t fg[64];
    uint16_t bg[64];
    size_t pos = 0U;
    size_t value_start;
    size_t mask_start;

    if (draw_frame) {
        draw_masked_serial_frame("H", "L");
        previous_header[0] = '\0';
        previous_status[0] = '\0';
        memset(previous_rx, 0, sizeof(previous_rx));
        previous_header_selected = false;
        previous_header_digit = 0xFFU;
        previous_header_blink = 0xFFU;
        previous_status_selected = false;
        previous_status_digit = 0xFFU;
        previous_status_blink = 0xFFU;
    }

    snprintf(value, sizeof(value), "%lu", (unsigned long)(s->control.can_bitrate / 1000U));
    fill_text_colors(fg, bg, 64U);
    append_colored(line, fg, bg, &pos, "CAN  BAUD ", COLOR_CYAN);
    value_start = pos;
    append_colored(line, fg, bg, &pos, value, COLOR_YELLOW);
    append_colored(line, fg, bg, &pos, " KBIT", COLOR_GREEN);
    bool header_selected = s->control.selected_value == CONTROL_SELECT_CAN_BITRATE;
    uint8_t header_blink = (uint8_t)((esp_timer_get_time() / 500000LL) & 1LL);
    if (header_selected) {
        bool blink_on = s->control.selected_digit == CONTROL_DIGIT_WHOLE ||
                        header_blink == 0U;
        if (blink_on) {
            mark_range(fg, bg, value_start, strlen(value), COLOR_BLACK, COLOR_YELLOW);
        }
    }
    if (strcmp(previous_header, line) != 0 ||
        previous_header_selected != header_selected ||
        previous_header_digit != s->control.selected_digit ||
        (header_selected &&
         s->control.selected_digit != CONTROL_DIGIT_WHOLE &&
         previous_header_blink != header_blink)) {
        fill_rect(8, 3, INTERFACE_MAIN_FRAME_WIDTH - 4, 21, COLOR_PANEL);
        draw_rich_text_on_panel_clipped(10, 4, line, &instrument_18, fg, bg,
                                        COLOR_PANEL, 8, INTERFACE_MAIN_INNER_RIGHT,
                                        3, 24);
        snprintf(previous_header, sizeof(previous_header), "%s", line);
        previous_header_selected = header_selected;
        previous_header_digit = s->control.selected_digit;
        previous_header_blink = header_blink;
    }

    line[0] = '\0';
    pos = 0U;
    fill_text_colors(fg, bg, 64U);
    append_colored(line, fg, bg, &pos, "MASK ", COLOR_LABEL);
    mask_start = pos;
    append_colored(line, fg, bg, &pos, s->control.can_mask, COLOR_YELLOW);
    append_colored(line, fg, bg, &pos, " TX ", COLOR_LABEL);
    append_format_colored(line, fg, bg, &pos, COLOR_YELLOW, "%lu",
                          (unsigned long)s->can.tx_queue_msgs);
    bool status_selected = s->control.selected_value == CONTROL_SELECT_CAN_MASK;
    uint8_t status_blink = (uint8_t)((esp_timer_get_time() / 500000LL) & 1LL);
    if (s->control.selected_value == CONTROL_SELECT_CAN_MASK) {
        if (s->control.selected_digit == CONTROL_DIGIT_WHOLE) {
            mark_range(fg, bg, mask_start, strlen(s->control.can_mask),
                       COLOR_BLACK, COLOR_YELLOW);
        } else if (s->control.selected_digit < strlen(s->control.can_mask) &&
                   status_blink == 0U) {
            mark_range(fg, bg, mask_start + s->control.selected_digit, 1U,
                       COLOR_BLACK, COLOR_YELLOW);
        }
    }
    if (strcmp(previous_status, line) != 0 ||
        previous_status_selected != status_selected ||
        previous_status_digit != s->control.selected_digit ||
        (status_selected &&
         s->control.selected_digit != CONTROL_DIGIT_WHOLE &&
         previous_status_blink != status_blink)) {
        fill_rect(8, 27, INTERFACE_MAIN_FRAME_WIDTH - 4, 21, COLOR_PANEL);
        draw_rich_text_on_panel_clipped(10, 27, line, &instrument_18, fg, bg,
                                        COLOR_PANEL, 8, INTERFACE_MAIN_INNER_RIGHT,
                                        25, 51);
        snprintf(previous_status, sizeof(previous_status), "%s", line);
        previous_status_selected = status_selected;
        previous_status_digit = s->control.selected_digit;
        previous_status_blink = status_blink;
    }

    const int rx_y[3] = {54, 76, 98};
    for (size_t i = 0U; i < 3U; ++i) {
        if (strcmp(previous_rx[i], s->can.lines[i]) == 0) continue;
        fill_rect(8, rx_y[i], INTERFACE_MAIN_FRAME_WIDTH - 4, 20, COLOR_PANEL);
        draw_small_rx_line(rx_y[i], s->can.lines[i], INTERFACE_MAIN_INNER_RIGHT);
        snprintf(previous_rx[i], sizeof(previous_rx[i]), "%s", s->can.lines[i]);
    }

    draw_bottom_actuals_to(s, INTERFACE_MAIN_INNER_RIGHT);
}

static void draw_setting_line(int x,
                              int y,
                              int panel_left,
                              int panel_right,
                              const char *label,
                              const char *value,
                              const char *suffix,
                              uint16_t suffix_color,
                              uint8_t select,
                              const app_state_t *s,
                              int clip_top,
                              int clip_bottom)
{
    char line[64] = "";
    uint16_t fg[64];
    uint16_t bg[64];
    size_t pos = 0U;
    size_t value_start;

    fill_text_colors(fg, bg, 64U);
    append_colored(line, fg, bg, &pos, label, COLOR_LABEL);
    append_colored(line, fg, bg, &pos, " ", COLOR_LABEL);
    value_start = pos;
    append_colored(line, fg, bg, &pos, value, COLOR_YELLOW);
    if (suffix != NULL && suffix[0] != '\0') {
        append_colored(line, fg, bg, &pos, suffix, suffix_color);
    }

    if (s->control.selected_value == select) {
        bool blink_on = ((esp_timer_get_time() / 500000LL) & 1LL) == 0LL;
        size_t value_length = strlen(value);
        if (s->control.selected_digit == CONTROL_DIGIT_WHOLE) {
            mark_range(fg, bg, value_start, value_length, COLOR_BLACK, COLOR_YELLOW);
        } else if ((select == CONTROL_SELECT_OVERCURRENT ||
                    select == CONTROL_SELECT_CALIBRATION ||
                    select == CONTROL_SELECT_OVERHEAT ||
                    select == CONTROL_SELECT_OVERPOWER ||
                    select == CONTROL_SELECT_VOLUME) && blink_on) {
            mark_range(fg, bg, value_start, value_length, COLOR_BLACK, COLOR_YELLOW);
        } else if (blink_on) {
            mark_range(fg,
                       bg,
                       value_start + editable_digit_offset(value, s->control.selected_digit),
                       1U,
                       COLOR_BLACK,
                       COLOR_YELLOW);
        }
    }

    draw_rich_text_on_panel_clipped(x, y, line, &instrument_18, fg, bg,
                                    COLOR_PANEL, panel_left, panel_right,
                                    clip_top, clip_bottom);
}

static void format_calibration_current(char *out, size_t size, int64_t current_ua)
{
    bool negative = current_ua < 0;
    if (negative) current_ua = -current_ua;
    int64_t ma_x1000 = current_ua;
    snprintf(out,
             size,
             "%s%lld.%03lldmA",
             negative ? "-" : "",
             (long long)(ma_x1000 / 1000LL),
             (long long)(ma_x1000 % 1000LL));
}

static void draw_plain_text_on_bg(int x,
                                  int y,
                                  const char *text,
                                  const smooth_font_t *font,
                                  uint16_t fg_color,
                                  uint16_t bg_color,
                                  int panel_left,
                                  int panel_right,
                                  int clip_top,
                                  int clip_bottom)
{
    char line[48];
    uint16_t fg[48];
    uint16_t bg[48];
    size_t pos = 0U;

    snprintf(line, sizeof(line), "%s", text);
    fill_text_colors(fg, bg, sizeof(fg) / sizeof(fg[0]));
    (void)pos;
    for (size_t i = 0U; i < strlen(line) && i < sizeof(fg) / sizeof(fg[0]); ++i) {
        fg[i] = fg_color;
        bg[i] = bg_color;
    }
    draw_rich_text_on_panel_clipped(x, y, line, font, fg, bg,
                                    bg_color, panel_left, panel_right,
                                    clip_top, clip_bottom);
}

static void draw_choice_button(int x, int y, const char *text, bool selected)
{
    uint16_t bg = selected ? COLOR_YELLOW : COLOR_PANEL;
    uint16_t fg = selected ? COLOR_BLACK : COLOR_LABEL;
    uint16_t outline = selected ? COLOR_YELLOW : COLOR_GRAY;
    fill_round_rect(x, y, 104, 32, 4, bg);
    fill_rect(x, y, 104, 2, outline);
    fill_rect(x, y + 30, 104, 2, outline);
    fill_rect(x, y, 2, 32, outline);
    fill_rect(x + 102, y, 2, 32, outline);
    int tx = x + (104 - text_width(text, &instrument_18)) / 2;
    draw_plain_text_on_bg(tx, y + 7, text, &instrument_18, fg, bg,
                          x, x + 104, y, y + 32);
}

static void draw_calibration_confirm_screen(const app_state_t *s, bool draw_frame)
{
    if (draw_frame) {
        fill_rect(0, 0, TFT_WIDTH, TFT_HEIGHT, COLOR_BLACK);
        draw_text(8, 5, "CALIBRATION", &instrument_18, COLOR_CYAN);
        fill_round_rect(8, 34, 304, 70, 4, COLOR_PANEL);
        draw_panel_outline(6, 32, 308, 74, COLOR_RED);
        int warning_x = 8 + (304 - text_width("DISCONNECT ALL OUTPUTS", &instrument_18)) / 2;
        draw_plain_text_on_bg(warning_x, 63, "DISCONNECT ALL OUTPUTS", &instrument_18, COLOR_RED,
                              COLOR_PANEL, 8, 312, 34, 104);
    }
    draw_choice_button(36, 126, "OK", s->control.calibration_confirm_ok);
    draw_choice_button(180, 126, "CANCEL", !s->control.calibration_confirm_ok);
}

static void draw_calibration_progress_screen(const app_state_t *s, bool draw_frame)
{
    static char previous_channel_line[40];
    static char previous_set_line[40];
    static char previous_meas_line[40];
    static char previous_current_line[40];
    static char previous_count_line[40];
    char line[40];
    char current[24];
    char channel = s->control.calibration_channel == 'B' ? 'B' : 'A';

    if (draw_frame) {
        fill_rect(0, 0, TFT_WIDTH, TFT_HEIGHT, COLOR_BLACK);
        draw_text(8, 5, "CALIBRATION", &instrument_18, COLOR_CYAN);
        fill_rect(8, 31, 304, 31, COLOR_BLACK);
        fill_round_rect(8, 70, 304, 90, 4, COLOR_PANEL);
        draw_panel_outline(6, 68, 308, 94, COLOR_CYAN);
        previous_channel_line[0] = '\0';
        previous_set_line[0] = '\0';
        previous_meas_line[0] = '\0';
        previous_current_line[0] = '\0';
        previous_count_line[0] = '\0';
    }

    snprintf(line, sizeof(line), "CHANNEL %c", channel);
    if (strcmp(previous_channel_line, line) != 0) {
        fill_rect(8, 31, 304, 31, COLOR_BLACK);
        draw_text(8, 31, line, &instrument_30, channel == 'A' ? COLOR_CYAN : COLOR_PURPLE);
        snprintf(previous_channel_line, sizeof(previous_channel_line), "%s", line);
    }

    snprintf(line,
             sizeof(line),
             "SET %u.%02uV",
             (unsigned)(s->control.calibration_target_mv / 1000U),
             (unsigned)((s->control.calibration_target_mv % 1000U) / 10U));
    if (strcmp(previous_set_line, line) != 0) {
        draw_plain_text_on_bg(16, 80, line, &instrument_18, COLOR_LABEL,
                              COLOR_PANEL, 8, 312, 70, 160);
        snprintf(previous_set_line, sizeof(previous_set_line), "%s", line);
    }

    snprintf(line,
             sizeof(line),
             "MEAS %lu.%02luV",
             (unsigned long)(s->control.calibration_measured_mv / 1000U),
             (unsigned long)((s->control.calibration_measured_mv % 1000U) / 10U));
    if (strcmp(previous_meas_line, line) != 0) {
        draw_plain_text_on_bg(16, 104, line, &instrument_18, COLOR_YELLOW,
                              COLOR_PANEL, 8, 312, 70, 160);
        snprintf(previous_meas_line, sizeof(previous_meas_line), "%s", line);
    }

    format_calibration_current(current,
                               sizeof(current),
                               s->control.calibration_measured_current_ua);
    snprintf(line, sizeof(line), "I %s", current);
    if (strcmp(previous_current_line, line) != 0) {
        draw_plain_text_on_bg(16, 128, line, &instrument_18, COLOR_LABEL,
                              COLOR_PANEL, 8, 312, 70, 160);
        snprintf(previous_current_line, sizeof(previous_current_line), "%s", line);
    }

    snprintf(line,
             sizeof(line),
             "%lu/%u",
             (unsigned long)s->control.calibration_sample_count,
             (unsigned)DISPLAY_CALIBRATION_SAMPLE_COUNT);
    if (strcmp(previous_count_line, line) != 0) {
        draw_plain_text_on_bg(242, 128, line, &instrument_18, COLOR_GRAY,
                              COLOR_PANEL, 8, 312, 70, 160);
        snprintf(previous_count_line, sizeof(previous_count_line), "%s", line);
    }
}

static int font_max_digit_width(const smooth_font_t *font)
{
    int max_width = 0;
    for (char c = '0'; c <= '9'; ++c) {
        char text[2] = {c, '\0'};
        int width = text_width(text, font);
        if (width > max_width) max_width = width;
    }
    return max_width;
}

static void buffer_draw_fixed_current_char(int x,
                                           int y,
                                           int slot_width,
                                           char c,
                                           const smooth_font_t *font,
                                           uint16_t fg,
                                           uint16_t bg,
                                           int buffer_height)
{
    char text[2] = {c, '\0'};
    int width = text_width(text, font);
    int char_x = x + (slot_width - width) / 2;
    buffer_draw_text(char_x, y, text, font, fg, bg, buffer_height);
}

static void draw_calibration_done_screen(void)
{
    fill_rect(0, 0, TFT_WIDTH, TFT_HEIGHT, COLOR_BLACK);
    fill_round_rect(18, 52, 284, 66, 4, COLOR_PANEL);
    draw_panel_outline(16, 50, 288, 70, COLOR_GREEN);
    draw_plain_text_on_bg(33, 72, "CALIBRATE DONE", &instrument_30,
                          COLOR_GREEN, COLOR_PANEL, 18, 302, 52, 118);
}

static void draw_setting_screen(const app_state_t *s, bool draw_frame)
{
    char value[8];

    if (s->control.calibration_done) {
        draw_calibration_done_screen();
        return;
    }
    if (s->control.calibration_running) {
        draw_calibration_progress_screen(s, draw_frame);
        return;
    }
    if (s->control.calibration_confirm) {
        draw_calibration_confirm_screen(s, draw_frame);
        return;
    }

    if (draw_frame) {
        fill_rect(0, 0, TFT_WIDTH, TFT_HEIGHT, COLOR_BLACK);
        fill_rect(8, 29, 146, 28, COLOR_PANEL);
        draw_panel_outline(6, 27, 150, 32, COLOR_CYAN);
        fill_rect(166, 29, 146, 28, COLOR_PANEL);
        draw_panel_outline(164, 27, 150, 32, COLOR_PURPLE);
        fill_rect(8, 65, 146, 28, COLOR_PANEL);
        draw_panel_outline(6, 63, 150, 32, COLOR_PURPLE);
        fill_rect(166, 65, 146, 28, COLOR_PANEL);
        draw_panel_outline(164, 63, 150, 32, COLOR_CYAN);
        fill_rect(8, 101, 146, 28, COLOR_PANEL);
        draw_panel_outline(6, 99, 150, 32, COLOR_CYAN);
    }
    if (draw_frame) {
        draw_text(8, 4, "SETTING", &instrument_18, COLOR_CYAN);
    }

    draw_setting_line(12, 31, 8, 154,
                      "Overcurrent",
                      s->control.overcurrent_cc ? "CC" : "TRG",
                      NULL,
                      COLOR_LABEL,
                      CONTROL_SELECT_OVERCURRENT,
                      s, 29, 57);
    snprintf(value, sizeof(value), "%02u", (unsigned)s->control.overheat_c);
    draw_setting_line(170, 31, 166, 312, "Overheat", value, NULL, COLOR_LABEL,
                      CONTROL_SELECT_OVERHEAT, s, 29, 57);
    if (s->control.overpower_w == 0U) snprintf(value, sizeof(value), "--");
    else snprintf(value, sizeof(value), "%u", (unsigned)s->control.overpower_w);
    draw_setting_line(12, 67, 8, 154, "Overpower", value, "W", COLOR_LABEL,
                      CONTROL_SELECT_OVERPOWER, s, 65, 93);
    snprintf(value, sizeof(value), "%u", (unsigned)s->control.volume_percent);
    draw_setting_line(170, 67, 166, 312, "Volume", value, NULL, COLOR_LABEL,
                      CONTROL_SELECT_VOLUME, s, 65, 93);
    draw_setting_line(12, 103, 8, 154,
                      "Calib",
                      s->control.calibration_on || s->control.calibration_running ? "ON" : "OFF",
                      NULL,
                      COLOR_LABEL,
                      CONTROL_SELECT_CALIBRATION,
                      s, 101, 129);
}

static const char *current_graph_channel_text(uint8_t channels)
{
    if (channels == CURRENT_GRAPH_CHANNEL_A) return "A";
    if (channels == CURRENT_GRAPH_CHANNEL_B) return "B";
    return "AB";
}

static void draw_graph_pixel(int x, int y, uint16_t color)
{
    if (x < CURRENT_GRAPH_X || x >= CURRENT_GRAPH_X + CURRENT_GRAPH_W ||
        y < s_graph_slice_y || y >= s_graph_slice_y + s_graph_slice_h) {
        return;
    }
    s_text_buffer[(y - s_graph_slice_y) * TFT_WIDTH + x] = display_pixel(color);
}

static void draw_graph_line(int x0, int y0, int x1, int y1, uint16_t color)
{
    int dx = x1 > x0 ? x1 - x0 : x0 - x1;
    int sx = x0 < x1 ? 1 : -1;
    int dy = y1 > y0 ? y0 - y1 : y1 - y0;
    int sy = y0 < y1 ? 1 : -1;
    int err = dx + dy;

    while (true) {
        draw_graph_pixel(x0, y0, color);
        if (x0 == x1 && y0 == y1) break;
        int e2 = 2 * err;
        if (e2 >= dy) {
            err += dy;
            x0 += sx;
        }
        if (e2 <= dx) {
            err += dx;
            y0 += sy;
        }
    }
}

static uint16_t current_graph_next_auto_scale(uint16_t scale_ma)
{
    switch (scale_ma) {
        case 10U: return 100U;
        case 100U: return 1000U;
        case 1000U: return 5000U;
        default: return 5000U;
    }
}

static uint16_t current_graph_previous_auto_scale(uint16_t scale_ma)
{
    switch (scale_ma) {
        case 5000U: return 1000U;
        case 1000U: return 100U;
        case 100U: return 10U;
        default: return 10U;
    }
}

static int32_t graph_abs_ma(int32_t value)
{
    return value < 0 ? -value : value;
}

static uint16_t current_graph_auto_scale(const current_graph_snapshot_t *graph,
                                         uint8_t channels)
{
    static uint16_t auto_scale_ma = 1000U;
    static uint8_t low_count;
    int32_t max_ma = 0;

    for (size_t i = 0U; i < graph->count; ++i) {
        if ((channels & CURRENT_GRAPH_CHANNEL_A) != 0U && graph->a_valid[i]) {
            int32_t value = graph_abs_ma(graph->a_ma[i]);
            if (value > max_ma) max_ma = value;
        }
        if ((channels & CURRENT_GRAPH_CHANNEL_B) != 0U && graph->b_valid[i]) {
            int32_t value = graph_abs_ma(graph->b_ma[i]);
            if (value > max_ma) max_ma = value;
        }
    }

    uint32_t full_scale_ma = auto_scale_ma;
    if (max_ma > (int32_t)(full_scale_ma * 9U / 10U)) {
        auto_scale_ma = current_graph_next_auto_scale(auto_scale_ma);
        low_count = 0U;
    } else if (max_ma < (int32_t)(full_scale_ma / 4U)) {
        if (low_count < 30U) ++low_count;
        if (low_count >= 30U) {
            auto_scale_ma = current_graph_previous_auto_scale(auto_scale_ma);
            low_count = 0U;
        }
    } else {
        low_count = 0U;
    }

    return auto_scale_ma;
}

static int graph_y_from_current(int32_t current_ma, uint16_t scale_ma)
{
    int usable = CURRENT_GRAPH_H - 4;
    uint32_t full_scale_ma;
    if (scale_ma == 0U) scale_ma = 1000U;
    full_scale_ma = scale_ma;
    if (current_ma < 0) current_ma = 0;
    if (current_ma > (int32_t)full_scale_ma) current_ma = (int32_t)full_scale_ma;
    int y = CURRENT_GRAPH_Y + CURRENT_GRAPH_H - 2 -
            (int)(((int64_t)current_ma * usable) / full_scale_ma);
    if (y < CURRENT_GRAPH_Y + 1) y = CURRENT_GRAPH_Y + 1;
    if (y > CURRENT_GRAPH_Y + CURRENT_GRAPH_H - 2) y = CURRENT_GRAPH_Y + CURRENT_GRAPH_H - 2;
    return y;
}

static void draw_current_graph_channel(const current_graph_snapshot_t *graph,
                                       bool channel_a,
                                       uint16_t color,
                                       uint16_t scale_ma)
{
    bool have_previous = false;
    int previous_x = 0;
    int previous_y = 0;
    size_t count = graph->count > CURRENT_GRAPH_W ? CURRENT_GRAPH_W : graph->count;
    size_t start = graph->count - count;

    for (size_t i = 0U; i < count; ++i) {
        size_t src = start + i;
        bool valid = channel_a ? graph->a_valid[src] : graph->b_valid[src];
        if (!valid) {
            have_previous = false;
            continue;
        }
        int32_t current_ma = channel_a ? graph->a_ma[src] : graph->b_ma[src];
        int x = CURRENT_GRAPH_X + CURRENT_GRAPH_W - (int)count + (int)i;
        int y = graph_y_from_current(current_ma, scale_ma);
        if (have_previous) draw_graph_line(previous_x, previous_y, x, y, color);
        else draw_graph_pixel(x, y, color);
        previous_x = x;
        previous_y = y;
        have_previous = true;
    }
}

static void format_current_div(uint16_t full_scale_ma,
                               char *value,
                               size_t value_size,
                               const char **unit)
{
    uint16_t ma_per_div = (uint16_t)(full_scale_ma / CURRENT_GRAPH_CELLS_Y);
    if (ma_per_div >= 1000U && (ma_per_div % 1000U) == 0U) {
        snprintf(value, value_size, "%u", (unsigned)(ma_per_div / 1000U));
        *unit = "A/div";
    } else {
        snprintf(value, value_size, "%u", (unsigned)ma_per_div);
        *unit = "mA/div";
    }
}

static void format_time_div(uint8_t decimation,
                            char *value,
                            size_t value_size,
                            const char **unit)
{
    uint32_t ms = (uint32_t)decimation * CURRENT_GRAPH_BASE_SAMPLE_MS *
                  CURRENT_GRAPH_SAMPLES_PER_DIV;
    if (ms < 1000U) {
        snprintf(value, value_size, "%lu", (unsigned long)ms);
        *unit = "ms/div";
    } else if ((ms % 1000U) == 0U) {
        snprintf(value, value_size, "%lu", (unsigned long)(ms / 1000U));
        *unit = "s/div";
    } else {
        snprintf(value, value_size, "%lu.%lu",
                 (unsigned long)(ms / 1000U),
                 (unsigned long)((ms % 1000U) / 100U));
        *unit = "s/div";
    }
}

static void draw_current_graph_header(const app_state_t *s, uint16_t scale_ma)
{
    char line[96] = "";
    char time_value[16];
    char current_value[16];
    const char *time_unit = "s/div";
    const char *current_unit = "mA/div";
    uint16_t fg[96];
    uint16_t bg[96];
    size_t pos = 0U;
    size_t rate_start;
    size_t rate_len;
    size_t scale_start;
    size_t scale_len;
    size_t ch_start;
    size_t ch_len;

    format_time_div(s->control.current_graph_decimation,
                    time_value,
                    sizeof(time_value),
                    &time_unit);
    format_current_div(scale_ma, current_value, sizeof(current_value), &current_unit);

    fill_text_colors(fg, bg, 96U);
    append_colored(line, fg, bg, &pos, "T", COLOR_RED);
    rate_start = pos;
    append_colored(line, fg, bg, &pos, time_value, COLOR_WHITE);
    append_colored(line, fg, bg, &pos, time_unit, COLOR_BLUE);
    rate_len = strlen(time_value) + strlen(time_unit);
    append_colored(line, fg, bg, &pos, "  I", COLOR_RED);
    scale_start = pos;
    if (s->control.current_graph_scale_ma == 0U) {
        append_colored(line, fg, bg, &pos, "auto ", COLOR_BLUE);
    }
    append_colored(line, fg, bg, &pos, current_value, COLOR_WHITE);
    append_colored(line, fg, bg, &pos, current_unit, COLOR_BLUE);
    scale_len = pos - scale_start;
    append_colored(line, fg, bg, &pos, "  CH", COLOR_RED);
    ch_start = pos;
    append_colored(line, fg, bg, &pos,
                   current_graph_channel_text(s->control.current_graph_channels),
                   COLOR_WHITE);
    ch_len = strlen(current_graph_channel_text(s->control.current_graph_channels));

    bool show_edit = s->control.selected_digit == CONTROL_DIGIT_WHOLE ||
                     ((esp_timer_get_time() / 500000LL) & 1LL) == 0LL;
    if (s->control.selected_value == CONTROL_SELECT_CURRENT_RATE && show_edit) {
        mark_range(fg, bg, rate_start, rate_len, COLOR_BLACK, COLOR_YELLOW);
    } else if (s->control.selected_value == CONTROL_SELECT_CURRENT_SCALE && show_edit) {
        mark_range(fg, bg, scale_start, scale_len, COLOR_BLACK, COLOR_YELLOW);
    } else if (s->control.selected_value == CONTROL_SELECT_CURRENT_CHANNEL && show_edit) {
        mark_range(fg, bg, ch_start, ch_len, COLOR_BLACK, COLOR_YELLOW);
    }

    draw_rich_text_on_panel_clipped(10, 4, line, &instrument_18, fg, bg,
                                    COLOR_PANEL, 8, INTERFACE_MAIN_INNER_RIGHT,
                                    3, 24);
}

static void draw_current_graph_screen(const app_state_t *s, bool draw_frame)
{
    current_graph_snapshot_t graph;
    uint16_t scale_ma;
    if (draw_frame) draw_interface_frame(false, "", "");

    current_graph_snapshot(&graph);
    scale_ma = s->control.current_graph_scale_ma != 0U ?
               s->control.current_graph_scale_ma :
               current_graph_auto_scale(&graph, s->control.current_graph_channels);
    draw_current_graph_header(s, scale_ma);

    for (int slice_y = CURRENT_GRAPH_Y;
         slice_y < CURRENT_GRAPH_Y + CURRENT_GRAPH_H;
         slice_y += (int)DISPLAY_BUFFER_ROWS) {
        int slice_h = CURRENT_GRAPH_Y + CURRENT_GRAPH_H - slice_y;
        if (slice_h > (int)DISPLAY_BUFFER_ROWS) slice_h = (int)DISPLAY_BUFFER_ROWS;
        s_graph_slice_y = slice_y;
        s_graph_slice_h = slice_h;

        buffer_fill_rect(CURRENT_GRAPH_X, 0, CURRENT_GRAPH_W, slice_h,
                         slice_h, COLOR_PANEL);
        for (int x = CURRENT_GRAPH_X;
             x < CURRENT_GRAPH_X + CURRENT_GRAPH_W;
             x += CURRENT_GRAPH_SAMPLES_PER_DIV) {
            for (int y = CURRENT_GRAPH_Y; y < CURRENT_GRAPH_Y + CURRENT_GRAPH_H; y += 4) {
                draw_graph_pixel(x, y, RGB565(125, 145, 180));
            }
        }
        for (int cell = 0; cell <= CURRENT_GRAPH_CELLS_Y; ++cell) {
            int y = CURRENT_GRAPH_Y +
                    (cell * (CURRENT_GRAPH_H - 1)) / CURRENT_GRAPH_CELLS_Y;
            for (int x = CURRENT_GRAPH_X; x < CURRENT_GRAPH_X + CURRENT_GRAPH_W; x += 4) {
                draw_graph_pixel(x, y, RGB565(125, 145, 180));
            }
        }
        for (int x = CURRENT_GRAPH_X; x < CURRENT_GRAPH_X + CURRENT_GRAPH_W; x += 2) {
            draw_graph_pixel(x, CURRENT_GRAPH_Y + CURRENT_GRAPH_H - 2, RGB565(155, 170, 195));
        }
        if ((s->control.current_graph_channels & CURRENT_GRAPH_CHANNEL_A) != 0U) {
            draw_current_graph_channel(&graph, true, COLOR_CYAN, scale_ma);
        }
        if ((s->control.current_graph_channels & CURRENT_GRAPH_CHANNEL_B) != 0U) {
            draw_current_graph_channel(&graph, false, COLOR_PURPLE, scale_ma);
        }
        send_text_buffer_region(CURRENT_GRAPH_X, slice_y, CURRENT_GRAPH_W, slice_h);
    }
    draw_bottom_actuals_to(s, INTERFACE_MAIN_INNER_RIGHT);
}

static const char *mode_menu_name(app_mode_t mode)
{
    switch (mode) {
        case APP_MODE_POWER_SUPPLY: return "POWER source";
        case APP_MODE_1WIRE:        return "CURRENT graph";
        case APP_MODE_GENERATOR:    return "GENERATOR";
        case APP_MODE_UART:         return "UART term";
        case APP_MODE_LIN:          return "LIN sniffer";
        case APP_MODE_CAN:          return "CAN term";
        case APP_MODE_RS485:        return "RS485 term";
        case APP_MODE_I2C:          return "I2C sniffer";
        case APP_MODE_I2C_MASTER:   return "I2C master";
        case APP_MODE_SETTING:      return "SETTING";
        default:                    return "?";
    }
}

static void draw_mode_menu(const app_state_t *s, bool force)
{
    const uint8_t rows_per_column = 5U;
    const int frame_x[2] = {4, 162};
    const int frame_width = 154;
    const int frame_height = 32;
    const int row_pitch = 33;
    static char previous_lines[APP_MODE_COUNT][64];
    static uint8_t previous_selected = 0xFFU;
    static app_mode_t previous_active = APP_MODE_COUNT;

    if (force) {
        fill_rect(0, 0, TFT_WIDTH, TFT_HEIGHT, COLOR_BLACK);
        for (uint8_t mode_index = 0U; mode_index < (uint8_t)APP_MODE_COUNT; ++mode_index) {
            int column = mode_index / rows_per_column;
            int row = mode_index % rows_per_column;
            int x = frame_x[column];
            int y = 3 + row * row_pitch;
            fill_rect(x + 2, y + 2, frame_width - 4, frame_height - 4, COLOR_PANEL);
            draw_panel_outline(x, y, frame_width, frame_height,
                               column == 0 ? COLOR_CYAN : COLOR_PURPLE);
            previous_lines[mode_index][0] = '\0';
        }
        previous_selected = 0xFFU;
        previous_active = APP_MODE_COUNT;
    }

    for (uint8_t mode_index = 0U; mode_index < (uint8_t)APP_MODE_COUNT; ++mode_index) {
        char line[64];
        uint16_t fg[64];
        uint16_t bg[64];
        size_t length;
        int column = mode_index / rows_per_column;
        int row = mode_index % rows_per_column;
        int x = frame_x[column];
        int y = 3 + row * row_pitch;
        bool selected = mode_index == s->control.menu_index;
        bool active = mode_index == (uint8_t)s->control.mode;

        snprintf(line, sizeof(line), "%c %s", active ? '*' : ' ', mode_menu_name((app_mode_t)mode_index));
        length = strlen(line);
        fill_text_colors(fg, bg, 64U);

        for (size_t i = 0U; i < length; ++i) {
            fg[i] = active ? COLOR_GREEN : COLOR_WHITE;
            bg[i] = COLOR_BLACK;
        }
        if (selected) {
            mark_range(fg, bg, 0U, length, COLOR_BLACK, COLOR_YELLOW);
        }

        bool selection_changed_here = mode_index == s->control.menu_index ||
                                      mode_index == previous_selected;
        bool active_changed_here = mode_index == (uint8_t)s->control.mode ||
                                   mode_index == (uint8_t)previous_active;

        if (force ||
            selection_changed_here ||
            active_changed_here ||
            strcmp(previous_lines[mode_index], line) != 0) {
            int text_y = text_visual_y(line, &instrument_18, y, frame_height);
            draw_rich_text_on_panel(x + 4, text_y,
                                    line, &instrument_18, fg, bg,
                                    COLOR_PANEL, x + 2, x + frame_width - 2);
            snprintf(previous_lines[mode_index], sizeof(previous_lines[mode_index]), "%s", line);
        }
    }
    previous_selected = s->control.menu_index;
    previous_active = s->control.mode;
}

/* draw_status_line
 * Inputs: app state.
 * Returns: none.
 * Does: draws the bottom power summary line for the power-supply screen.
 */
static void draw_status_line(const app_state_t *s)
{
    char left[32] = "";
    char right[24] = "";
    uint16_t left_fg[32];
    uint16_t left_bg[32];
    uint16_t right_fg[24];
    uint16_t right_bg[24];
    size_t left_pos = 0U;
    size_t right_pos = 0U;
    const app_ina238_channel_t *a = &s->ina238.channel[0];
    const app_ina238_channel_t *b = &s->ina238.channel[1];
    bool temperature_valid = a->valid || b->valid;
    int32_t temperature_mc = 0;
    if (a->valid && b->valid) {
        temperature_mc = a->temperature_mc > b->temperature_mc ?
                         a->temperature_mc : b->temperature_mc;
    } else if (a->valid) {
        temperature_mc = a->temperature_mc;
    } else if (b->valid) {
        temperature_mc = b->temperature_mc;
    }
    uint32_t input_mv = s->analog.input_mv;
    uint32_t input_tenths = (input_mv + 50U) / 100U;
    uint32_t frequency_hz = s->timing.frequency_hz > 999999.0f ?
                            999999U : (uint32_t)(s->timing.frequency_hz + 0.5f);

    fill_text_colors(left_fg, left_bg, 32U);
    append_colored(left, left_fg, left_bg, &left_pos, "T", COLOR_GRAY);
    size_t temperature_start = left_pos;
    if (temperature_valid) {
        append_format_colored(left, left_fg, left_bg, &left_pos, COLOR_WHITE,
                              "%.0f", (double)temperature_mc / 1000.0);
    } else {
        append_colored(left, left_fg, left_bg, &left_pos, "--", COLOR_WHITE);
    }
    if (temperature_valid &&
        temperature_mc >= (int32_t)s->control.overheat_c * 1000) {
        mark_range(left_fg, left_bg, temperature_start,
                   left_pos - temperature_start,
                   COLOR_ALERT_RED_FG, COLOR_ALERT_RED_BG);
    }
    append_colored(left, left_fg, left_bg, &left_pos, "C ", COLOR_GREEN);
    append_colored(left, left_fg, left_bg, &left_pos, "V_IN", COLOR_GRAY);
    append_format_colored(left, left_fg, left_bg, &left_pos, COLOR_WHITE,
                          "%02lu.%01lu",
                          (unsigned long)(input_tenths / 10U),
                          (unsigned long)(input_tenths % 10U));
    append_colored(left, left_fg, left_bg, &left_pos, "V", COLOR_GREEN);

    fill_text_colors(right_fg, right_bg, 24U);
    append_colored(right, right_fg, right_bg, &right_pos, "FREQ ", COLOR_GRAY);
    append_format_colored(right, right_fg, right_bg, &right_pos, COLOR_WHITE,
                          "%06lu", (unsigned long)frequency_hz);
    append_colored(right, right_fg, right_bg, &right_pos, "Hz", COLOR_GREEN);

    int left_y = text_visual_y(left, &instrument_18, 140, 29);
    int right_y = text_visual_y(right, &instrument_18, 140, 29);
    draw_rich_text_on_panel_clipped(10, left_y, left, &instrument_18,
                                    left_fg, left_bg, COLOR_PANEL,
                                    8, 156, 142, 167);
    draw_rich_text_on_panel_clipped(166, right_y, right, &instrument_18,
                                    right_fg, right_bg, COLOR_PANEL,
                                    164, 312, 142, 167);
}

static uint16_t probe_voltage_badge_color(uint32_t voltage_mv, uint32_t test_span_mv)
{
    if (voltage_mv < 800U) return COLOR_GREEN;
    if (voltage_mv > 2200U) return COLOR_RED;
    if (test_span_mv < 88U) return COLOR_YELLOW;
    return COLOR_GRAY;
}

static void draw_power_probe_label(void)
{
    int inner_x = POWER_SIDE_FRAME_X + 2;
    int inner_width = POWER_SIDE_FRAME_WIDTH - 4;
    int label_x = inner_x + (inner_width - text_width("PRB", &instrument_18)) / 2;
    int label_y = text_visual_y("PRB", &instrument_18, 6, 23);
    uint16_t fg[4];
    uint16_t bg[4];
    fill_text_colors(fg, bg, 4U);
    mark_range(fg, bg, 0U, 3U, COLOR_GRAY, COLOR_PANEL);
    draw_rich_text_on_panel_clipped(label_x, label_y, "PRB", &instrument_18,
                                    fg, bg, COLOR_PANEL,
                                    inner_x, inner_x + inner_width, 4, 29);
}

static void format_probe_voltage(char *out, size_t size, uint32_t tenths)
{
    if (tenths > 999U) tenths = 999U;
    snprintf(out, size, "%lu.%01lu",
             (unsigned long)(tenths / 10U),
             (unsigned long)(tenths % 10U));
}

static void draw_power_probe_badge(uint32_t voltage_mv,
                                   uint32_t test_span_mv,
                                   uint32_t voltage_tenths)
{
    char value[8];
    uint16_t fg[8];
    uint16_t bg[8];
    int inner_x = POWER_SIDE_FRAME_X + 2;
    int inner_width = POWER_SIDE_FRAME_WIDTH - 4;
    int badge_size = inner_width - 6;
    int badge_x = inner_x + (inner_width - badge_size) / 2;
    uint16_t badge_color = probe_voltage_badge_color(voltage_mv, test_span_mv);

    fill_round_rect(badge_x, 31, badge_size, badge_size, 3,
                    badge_color);

    format_probe_voltage(value, sizeof(value), voltage_tenths);
    fill_text_colors(fg, bg, 12U);
    mark_range(fg, bg, 0U, strlen(value), COLOR_BLACK, badge_color);
    int value_x = inner_x + (inner_width - text_width(value, &instrument_30)) / 2;
    int value_y = text_visual_y(value, &instrument_30, 31, badge_size);
    draw_rich_text_on_panel_clipped(value_x, value_y, value, &instrument_30,
                                    fg, bg, badge_color,
                                    badge_x, badge_x + badge_size,
                                    31, 31 + badge_size);
}

static void format_probe_resistance(char *out, size_t size, uint32_t span_mv)
{
    const uint32_t source_ohm = PROBE_SYNC_SOURCE_OHM;
    const uint32_t open_span_mv = PROBE_SYNC_OPEN_SPAN_MV;
    const uint32_t source_mv = 3300U;

    if (span_mv == 0U || open_span_mv == 0U ||
        open_span_mv >= source_mv || span_mv >= open_span_mv) {
        snprintf(out, size, "--");
        return;
    }

    uint64_t base_ohm = ((uint64_t)source_ohm * open_span_mv +
                         (source_mv - open_span_mv) / 2U) /
                        (source_mv - open_span_mv);
    uint64_t equivalent_ohm = ((uint64_t)source_ohm * span_mv +
                               (source_mv - span_mv) / 2U) /
                              (source_mv - span_mv);

    if (base_ohm == 0U || equivalent_ohm >= base_ohm) {
        snprintf(out, size, "--");
        return;
    }

    uint64_t external_ohm = (equivalent_ohm * base_ohm +
                             (base_ohm - equivalent_ohm) / 2U) /
                            (base_ohm - equivalent_ohm);
    if (external_ohm > 50000U) {
        snprintf(out, size, "--");
    } else if (external_ohm < 1000U) {
        snprintf(out, size, "0k");
    } else {
        snprintf(out, size, "%luk", (unsigned long)((external_ohm + 500U) / 1000U));
    }
}

static void draw_power_probe_span(uint32_t span_mv)
{
    char value[12];
    uint16_t fg[12];
    uint16_t bg[12];
    int inner_x = POWER_SIDE_FRAME_X + 2;
    int inner_width = POWER_SIDE_FRAME_WIDTH - 4;
    format_probe_resistance(value, sizeof(value), span_mv);
    fill_text_colors(fg, bg, 8U);
    mark_range(fg, bg, 0U, strlen(value), COLOR_WHITE, COLOR_PANEL);
    int value_x = inner_x + (inner_width - text_width(value, &instrument_18)) / 2;
    int value_y = text_visual_y(value, &instrument_18, 94, 38);
    draw_rich_text_on_panel_clipped(value_x, value_y, value, &instrument_18,
                                    fg, bg, COLOR_PANEL,
                                    inner_x, inner_x + inner_width, 94, 132);
}

/* format_voltage
 * Inputs: destination buffer and voltage in millivolts.
 * Returns: none.
 * Does: writes a fixed xx.xx voltage string.
 */
static void format_voltage(char *out, size_t size, uint16_t mv)
{
    snprintf(out, size, "%02u.%02u", (unsigned)(mv / 1000U), (unsigned)((mv % 1000U) / 10U));
}

/* format_current
 * Inputs: destination buffer and current in milliamps.
 * Returns: none.
 * Does: writes a fixed x.xx current string.
 */
static void format_current(char *out, size_t size, uint16_t ma)
{
    snprintf(out, size, "%u.%02u", (unsigned)(ma / 1000U), (unsigned)((ma % 1000U) / 10U));
}

/* editable_digit_offset
 * Inputs: formatted numeric text and editable digit number.
 * Returns: character offset of the editable digit.
 * Does: skips the decimal point in fixed xx.xx/x.xx strings.
 */
static size_t editable_digit_offset(const char *value, uint8_t digit)
{
    size_t seen_digits = 0U;
    for (size_t i = 0U; value[i] != '\0'; ++i) {
        if (value[i] >= '0' && value[i] <= '9') {
            if (seen_digits == digit) return i;
            ++seen_digits;
        }
    }
    return 0U;
}

/* display_init
 * Inputs: none.
 * Returns: ESP_OK on success, or an ESP-IDF SPI/GPIO setup error.
 * Does: configures TFT pins, initializes ST7789 and draws the startup UI.
 */
esp_err_t display_init(void)
{
    ESP_LOGI(TAG, "init start: ST7789 %dx%d offset=%d,%d spi SCL=%d SDA=%d RES=%d DC=%d CS=%d BLK=%d active=%d",
             TFT_WIDTH,
             TFT_HEIGHT,
             TFT_X_OFFSET,
             TFT_Y_OFFSET,
             TFT_SCLK_GPIO,
             TFT_MOSI_GPIO,
             TFT_RESET_GPIO,
             TFT_DC_GPIO,
             TFT_CS_GPIO,
             TFT_BACKLIGHT_GPIO,
             TFT_BACKLIGHT_ACTIVE_LEVEL);
    gpio_config_t outputs = {
        .pin_bit_mask = (1ULL << TFT_DC_GPIO) | (1ULL << TFT_RESET_GPIO) |
                        (1ULL << TFT_CS_GPIO) | (1ULL << TFT_SCLK_GPIO) |
                        (1ULL << TFT_MOSI_GPIO) | (1ULL << TFT_BACKLIGHT_GPIO),
        .mode = GPIO_MODE_OUTPUT
    };
    ESP_ERROR_CHECK(gpio_config(&outputs));
    gpio_set_level(TFT_CS_GPIO, 1);
    gpio_set_level(TFT_DC_GPIO, 1);
    gpio_set_level(TFT_SCLK_GPIO, 0);
    gpio_set_level(TFT_MOSI_GPIO, 0);
    gpio_set_level(TFT_RESET_GPIO, 1);
    gpio_set_level(TFT_BACKLIGHT_GPIO, !TFT_BACKLIGHT_ACTIVE_LEVEL);
    ESP_RETURN_ON_ERROR(backlight_pwm_init(), TAG, "backlight init");
    log_pin_levels("after gpio defaults");
#if RGB_LED_ENABLED
    gpio_set_level(RGB_RED_GPIO, !RGB_ACTIVE_LEVEL);
    gpio_set_level(RGB_GREEN_GPIO, !RGB_ACTIVE_LEVEL);
    gpio_set_level(RGB_BLUE_GPIO, !RGB_ACTIVE_LEVEL);
#endif

    spi_bus_config_t bus = {
        .mosi_io_num = TFT_MOSI_GPIO,
        .miso_io_num = TFT_MISO_GPIO,
        .sclk_io_num = TFT_SCLK_GPIO,
        .quadwp_io_num = -1,
        .quadhd_io_num = -1,
        .max_transfer_sz = 4096
    };
    esp_err_t err = spi_bus_initialize(SPI2_HOST, &bus, SPI_DMA_CH_AUTO);
    if (err != ESP_OK) {
        ESP_LOGE(TAG, "spi bus init: %s", esp_err_to_name(err));
        log_pin_levels("after spi bus fail");
        return ESP_OK;
    }
    ESP_LOGI(TAG, "spi bus ok");
    spi_device_interface_config_t device = {
        .clock_speed_hz = 10000000,
        .mode = 0,
        .spics_io_num = TFT_CS_GPIO,
        .queue_size = 1
    };
    err = spi_bus_add_device(SPI2_HOST, &device, &s_tft);
    if (err != ESP_OK) {
        ESP_LOGE(TAG, "spi device add: %s", esp_err_to_name(err));
        log_pin_levels("after spi device fail");
        return ESP_OK;
    }
    ESP_LOGI(TAG, "spi device ok");

    gpio_set_level(TFT_RESET_GPIO, 0);
    vTaskDelay(pdMS_TO_TICKS(20));
    gpio_set_level(TFT_RESET_GPIO, 1);
    vTaskDelay(pdMS_TO_TICKS(120));
    log_pin_levels("after reset pulse");

    ESP_LOGI(TAG, "cmd SWRESET");
    command(0x01);
    vTaskDelay(pdMS_TO_TICKS(120));
    ESP_LOGI(TAG, "cmd SLPOUT");
    command(0x11);
    vTaskDelay(pdMS_TO_TICKS(120));
    ESP_LOGI(TAG, "cmd COLMOD/MADCTL/INVOFF/NORON/DISPON");
    const uint8_t format[] = {0x55}; command_data(0x3A, format, sizeof(format));
    const uint8_t madctl[] = {0x60}; command_data(0x36, madctl, sizeof(madctl));
    command(0x20);
    command(0x13);
    command(0x29);
    log_pin_levels("after display on");

    ESP_LOGI(TAG, "draw startup splash");
    draw_splash_bitmap();
    backlight_fade_in();
    vTaskDelay(pdMS_TO_TICKS(TFT_SPLASH_VISIBLE_MS - TFT_BACKLIGHT_FADE_MS));
    ESP_LOGI(TAG, "init done");
    return ESP_OK;
}

/* display_black
 * Inputs: none.
 * Returns: none.
 * Does: clears the entire TFT to black.
 */
void display_black (void){
    fill_rect(0, 0, TFT_WIDTH, TFT_HEIGHT, COLOR_BLACK);

}

/* display_set_rgb
 * Inputs: probe logic state.
 * Returns: none.
 * Does: drives the active-low onboard RGB LED according to logic state.
 */
void display_set_rgb(probe_logic_state_t state)
{
#if RGB_LED_ENABLED
    bool red = false, green = false, blue = false;
    switch (state) {
        case PROBE_LOW: green = true; break;
        case PROBE_HIGH: red = true; break;
        case PROBE_OPEN: break;
        case PROBE_OVERVOLTAGE: red = true; break;
        default: red = true; green = true; break;
    }
    gpio_set_level(RGB_RED_GPIO, red ? RGB_ACTIVE_LEVEL : !RGB_ACTIVE_LEVEL);
    gpio_set_level(RGB_GREEN_GPIO, green ? RGB_ACTIVE_LEVEL : !RGB_ACTIVE_LEVEL);
    gpio_set_level(RGB_BLUE_GPIO, blue ? RGB_ACTIVE_LEVEL : !RGB_ACTIVE_LEVEL);
#else
    (void)state;
#endif
}
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
