rcslon3-svg/DOGS2_v1/software/src/smooth_font.c

#include "smooth_font.h"

static const uint8_t instrument_14_bitmap[] = {
    0xA6, 0xA6, 0xA6, 0xA6, 0xA6, 0xA6, 0xA6, 0x00, 0x00, 0xAA, 0xF3, 0xF6, 0xF3, 0xF6, 0xF3, 0xF6,
    0x00, 0x0D, 0x30, 0xF1, 0x00, 0x00, 0xF1, 0x1F, 0x00, 0x0F, 0xFF, 0xFF, 0xFF, 0x30, 0x05, 0xA0,
    0x68, 0x00, 0x00, 0x67, 0x09, 0x60, 0x00, 0x0A, 0x50, 0xB3, 0x00, 0x00, 0xD3, 0x0F, 0x10, 0x06,
    0xFF, 0xFF, 0xFF, 0xA0, 0x03, 0xD0, 0x4A, 0x00, 0x00, 0x5A, 0x06, 0x80, 0x00, 0x00, 0x0A, 0xA0,
    0x00, 0x01, 0x9F, 0xFB, 0x60, 0x09, 0xDB, 0xA5, 0x80, 0x0F, 0x6A, 0xA0, 0x00, 0x0F, 0x9A, 0xA0,
    0x00, 0x07, 0xFF, 0xD5, 0x10, 0x00, 0x4D, 0xFF, 0xB0, 0x00, 0x0A, 0xA4, 0xF3, 0x08, 0x0A, 0xA3,
    0xF3, 0x2F, 0x8B, 0xB8, 0xF1, 0x02, 0x9F, 0xFB, 0x30, 0x00, 0x0A, 0xA0, 0x00, 0x1B, 0xF6, 0x00,
    0x5B, 0x03, 0xB3, 0xF0, 0x1F, 0x30, 0x3B, 0x3F, 0x06, 0xA0, 0x01, 0xBF, 0x61, 0xF2, 0x00, 0x00,
    0x00, 0x78, 0x00, 0x00, 0x00, 0x1F, 0x10, 0x00, 0x00, 0x08, 0x71, 0xDF, 0x60, 0x03, 0xF1, 0x5B,
    0x3F, 0x00, 0xA6, 0x05, 0xB3, 0xF0, 0x3F, 0x10, 0x1D, 0xF6, 0x02, 0xDF, 0xD2, 0x00, 0x0F, 0x70,
    0x7F, 0x00, 0x2F, 0x30, 0x3F, 0x20, 0x0F, 0x50, 0x00, 0x00, 0x0D, 0xF1, 0x00, 0x00, 0x7F, 0xFB,
    0x13, 0xF3, 0xF5, 0x2F, 0xA4, 0xF0, 0xF3, 0x04, 0xFF, 0xA0, 0xD9, 0x10, 0x9F, 0x90, 0x2A, 0xFF,
    0x96, 0xF5, 0x6F, 0x6F, 0x6F, 0x00, 0xA2, 0x06, 0xF2, 0x1F, 0x60, 0x5F, 0x10, 0x7A, 0x00, 0xA7,
    0x00, 0xA6, 0x00, 0xA7, 0x00, 0x7A, 0x00, 0x5F, 0x10, 0x1F, 0x60, 0x06, 0xF2, 0x00, 0xA2, 0x57,
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
    {3611, 16, 21, 20, 2, 3},
    {3779, 15, 21, 19, 2, 3},
    {3937, 16, 21, 20, 2, 3},
    {4105, 15, 21, 18, 2, 3},
    {4263, 14, 21, 17, 2, 3},
    {4410, 16, 21, 20, 2, 3},
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
};
const smooth_font_t instrument_30 = {instrument_30_bitmap, instrument_30_glyphs, 32, 126, 38};
