rcslon3-svg/DOGS2_v1/software/src/generator_output.c

#include "generator_output.h"

#include "driver/gpio.h"
#include "driver/ledc.h"
#include "esp_check.h"
#include "esp_timer.h"
#include "nvs.h"
#include "probe_config.h"

#define GENERATOR_NVS_NAMESPACE "generator"
#define GENERATOR_SAVE_DELAY_US 1000000LL
#define GENERATOR_LEDC_SOURCE_HZ 80000000ULL
#define GENERATOR_LEDC_MODE LEDC_HIGH_SPEED_MODE
#define GENERATOR_LEDC_TIMER LEDC_TIMER_1
#define GENERATOR_LEDC_CHANNEL LEDC_CHANNEL_1

static generator_output_state_t s_state = {
    .frequency_hz = 1000U,
    .duty_percent = 50U,
    .enabled = false,
};
static bool s_dirty;
static int64_t s_last_change_us;

static uint32_t clamp_u32(uint32_t value, uint32_t minimum, uint32_t maximum)
{
    if (value < minimum) return minimum;
    if (value > maximum) return maximum;
    return value;
}

static uint8_t clamp_u8(uint8_t value, uint8_t minimum, uint8_t maximum)
{
    if (value < minimum) return minimum;
    if (value > maximum) return maximum;
    return value;
}

static ledc_timer_bit_t select_ledc_resolution(uint32_t frequency_hz)
{
    uint32_t bits = 10U;
    while (bits > 1U && ((uint64_t)frequency_hz << bits) > GENERATOR_LEDC_SOURCE_HZ) {
        --bits;
    }
    return (ledc_timer_bit_t)bits;
}

static esp_err_t drive_low(void)
{
    (void)ledc_stop(GENERATOR_LEDC_MODE, GENERATOR_LEDC_CHANNEL, 0);
    gpio_config_t output = {
        .pin_bit_mask = (1ULL << GENERATOR_OUTPUT_GPIO),
        .mode = GPIO_MODE_OUTPUT,
        .pull_up_en = GPIO_PULLUP_DISABLE,
        .pull_down_en = GPIO_PULLDOWN_DISABLE,
        .intr_type = GPIO_INTR_DISABLE,
    };
    ESP_RETURN_ON_ERROR(gpio_config(&output), "generator", "gpio config");
    gpio_set_level(GENERATOR_OUTPUT_GPIO, 0);
    return ESP_OK;
}

static esp_err_t apply_output(void)
{
    if (!s_state.enabled) return drive_low();

    gpio_reset_pin(GENERATOR_OUTPUT_GPIO);

    ledc_timer_bit_t resolution = select_ledc_resolution(s_state.frequency_hz);
    ledc_timer_config_t timer = {
        .speed_mode = GENERATOR_LEDC_MODE,
        .timer_num = GENERATOR_LEDC_TIMER,
        .duty_resolution = resolution,
        .freq_hz = s_state.frequency_hz,
        .clk_cfg = LEDC_AUTO_CLK,
    };
    ESP_RETURN_ON_ERROR(ledc_timer_config(&timer), "generator", "ledc timer");

    uint32_t duty_steps = 1UL << (uint32_t)resolution;
    uint32_t ledc_duty = (duty_steps * (uint32_t)s_state.duty_percent + 50U) / 100U;
    if (ledc_duty >= duty_steps) ledc_duty = duty_steps - 1U;

    ledc_channel_config_t channel = {
        .gpio_num = GENERATOR_OUTPUT_GPIO,
        .speed_mode = GENERATOR_LEDC_MODE,
        .channel = GENERATOR_LEDC_CHANNEL,
        .intr_type = LEDC_INTR_DISABLE,
        .timer_sel = GENERATOR_LEDC_TIMER,
        .duty = ledc_duty,
        .hpoint = 0,
    };
    ESP_RETURN_ON_ERROR(ledc_channel_config(&channel), "generator", "ledc channel");
    ESP_RETURN_ON_ERROR(ledc_set_duty(GENERATOR_LEDC_MODE,
                                      GENERATOR_LEDC_CHANNEL,
                                      ledc_duty),
                        "generator", "ledc duty");
    return ledc_update_duty(GENERATOR_LEDC_MODE, GENERATOR_LEDC_CHANNEL);
}

static void load_state(void)
{
    nvs_handle_t nvs;
    if (nvs_open(GENERATOR_NVS_NAMESPACE, NVS_READONLY, &nvs) != ESP_OK) return;

    uint32_t frequency = 0;
    uint8_t duty = 0;
    uint8_t enabled = 0;
    if (nvs_get_u32(nvs, "freq", &frequency) == ESP_OK) {
        s_state.frequency_hz = clamp_u32(frequency, GENERATOR_FREQ_MIN_HZ, GENERATOR_FREQ_MAX_HZ);
    }
    if (nvs_get_u8(nvs, "duty", &duty) == ESP_OK) {
        s_state.duty_percent = clamp_u8(duty, GENERATOR_DUTY_MIN_PERCENT, GENERATOR_DUTY_MAX_PERCENT);
    }
    if (nvs_get_u8(nvs, "on", &enabled) == ESP_OK) {
        s_state.enabled = enabled != 0U;
    }

    nvs_close(nvs);
}
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
